kkrzysztofik/ASG_AirsoftCounter/docs/plans/2026-10-02-lipo-board-implementation.md

# LiPo Board (hardware) Implementation Plan

> **For Claude:** REQUIRED SUB-SKILL: Use superpowers:executing-plans to implement this plan task-by-task.

**Goal:** A JLCPCB-ready 2S/3S LiPo power board (`hardware/lipo.*`, `hardware/fab/lipo/`) generated by the
same flow as the carrier and the pack boards, as specified in `docs/plans/2026-10-02-lipo-board-design.md`.
LiPo firmware is out of scope (deferred with the pack firmware).

**Architecture:** A new board module `hardware/lipo.py`, selected by `BOARD=lipo` through `board.py`. It is
standalone (it shares almost nothing with the cell pack): it imports only footprint constants and `_tags`
from `pack.py`. Its own `check_power_path()` asserts the input -> fuse -> reverse FET -> TVS -> bucks order
and the EN wiring, next to the shared `board.check_structure`. Schematic, PCB, routing, ERC/DRC and the fab
package come from the existing generators unchanged.

**Tech stack:** Python 3 (`/usr/bin/python3`, needed for `pcbnew`), KiCad 9.0.8 (`kicad-cli`, pcbnew API),
Freerouting 2.4.1 (`hardware/tools/`), GNU make. JLCPCB parts API for stock checks.

**Conventions (read before starting):**
- Run everything from `hardware/`. Use `/usr/bin/python3` (`pcbnew` lives in the system Python).
- `rtk` rewrites some output; use plain `make`, `/usr/bin/grep -F`, `diff` when you need exact output.
- Every LCSC number is checked live before it goes into the module, and its comment records type
  (B = Basic, P = Preferred, E = Extended), maker part and date. Stock query:

  ```bash
  curl -sS -m 20 -X POST 'https://jlcpcb.com/api/overseas-pcb-order/v1/shoppingCart/smtGood/selectSmtComponentList' \
    -H 'Content-Type: application/json' -d '{"keyword":"TPS54302DDCR","currentPage":1,"pageSize":6}' \
    | /usr/bin/python3 -c 'import sys,json; [print(p["componentCode"],p["componentModelEn"],p["componentLibraryType"],p["stockCount"],p["componentSpecificationEn"]) for p in json.load(sys.stdin)["data"]["componentPageInfo"]["list"]]'
  ```
- Commit after every task. End commit messages with the attribution line in use for this repo.
- Pin numbers below come from the KiCad 9 symbols, checked 2026-10-02: TPS54302 1 GND, 2 SW, 3 VIN, 4 FB,
  5 EN, 6 BOOT; HT75xx-1-SOT89 1 GND, 2 VIN, 3 VOUT; AO3401A/BSS138 1 G, 2 S, 3 D; Device diodes 1 K, 2 A.
  STM32C071KBTx (LQFP32) pins reuse the roles variant A already checked: 4 VDD, 5 VSS, 6 NRST,
  7/8/9 PA0-PA2 (ADC), 13/14 I2C slave SDA/SCL, 15 PB0, 24 SWDIO, 25 SWCLK/BOOT0.

## Changes against the design doc (record them in it in L0.1)

- **Balance dividers always on**, no divider switch and no separate pack-total divider. With Basic
  megohm values they draw about 10 uA, next to the MCU's 85 uA Stop current; the top tap already is
  the pack total. Each ADC pin gets 100 nF so the STM32 ADC sees a low source impedance.
- **No reset/boot buttons and no status LED**: SWD pads only (a blank STM32C0 boots its ROM
  bootloader by itself). Saves the TACT and LED and their drain.
- **Bucks default ON when the key is on**: the kill FET's gate has a pull-down, so the bucks run with
  the MCU unflashed (bring-up) and the firmware latches them off.
- **Same inductor for both bucks if L0.1 confirms its saturation current** covers buck A's peaks
  (Heltec ~1 A at 27 dBm + amp 1.5 A, see `power_budget.py`); otherwise buck A gets its own part.

---

## Phase L0: part facts (gates the schematic)

### Task L0.1: Verify datasheet facts, record them in the design doc

No code. Output: a "Parts" section appended to `docs/plans/2026-10-02-lipo-board-design.md` (one row
per item: decision, source, date), the four changes above recorded, and its "Unverified" list trimmed.

Check and record (datasheet section or table for each):

1. **TPS54302** (C311983): VIN range and absolute max (expect 4.5-28 V, 30 V abs), VREF (expect 0.596 V),
   EN rising threshold, EN pull-up current and EN absolute max (the EN node sees up to
   13.05 V x 47k/147k = 4.2 V, more on a hot-plug spike), shutdown current, current limit, maximum duty
   cycle at 6 V in / 4.1 V out, recommended inductor and output capacitance for 4.1 V and 5.07 V.
2. **Feedback dividers:** buck A 30k/5k1 -> 0.596 x (1 + 30/5.1) = 4.10 V; buck B 75k/10k -> 5.07 V.
   Confirm both against VREF and the datasheet's allowed bottom-resistor range.
3. **Inductor:** `10uH 2A` (C2046332, Bourns SRN6045TA-100M) Isat and Irms against the TPS54302 current
   limit. If Isat is below about 3 A, pick a 10 uH part with Isat >= 3.5 A for buck A (`L_A`) and record it.
4. **HT7533-1** (C14289, Basic, SOT-89-3): VIN absolute max (must survive 3S full plus the hot-plug
   spike after the TVS), Iq, required input/output capacitors. If VIN max is below the TVS clamp,
   add a 1k series resistor before `C_LDO1` (the LDO draws microamps) and record why.
5. **AO3407A** (C15155): VDS -30 V, VGS +-20 V, RDS(on) at VGS -4.5 V (2S empty, about 6 V), pinout
   G-S-D the same as the AO3401A symbol used for it.
6. **SMBJ15A** (C113988): standoff 15 V (above 3S 12.6 V), clamp at the pack's hot-plug energy.
   Drawn with `Device:D_Zener` (unidirectional, K to the rail).
7. **BZT52C12** gate clamp (C43491, E): look for a Basic or Preferred 12 V SOD-123 zener first.
8. **Solder pads** `Connector_Wire:SolderWire-1sqmm_1x02_P5.4mm_D1.4mm_OD2.7mm`: 1 mm2 (17 AWG) is enough
   for the ~3 A worst case at 2S empty; a 14 AWG XT60 pigtail needs the 1.5 mm2 / 1.7 mm-drill
   variant. Pick one, record the lead gauge.
9. **B4B-XH-A** (balance): the carrier's C144395. Confirm a 3-pin XH plug seats in pins 1-3 of a
   4-pin header (keyed housing ramp on one side only); if not, fit B3B-XH-A + B4B-XH-A side by side.
10. **Divider values** (Basic 1M C17514, 470k C17709): tap1 470k/1M -> x0.680 (4.35 V -> 2.96 V),
   tap2 1M/470k -> x0.320 (8.70 V -> 2.78 V), tap3 2x1M/470k -> x0.190 (13.05 V -> 2.48 V). All below
   the 3.3 V ADC reference with HV-LiPo margin.

Commit: `docs: LiPo board part facts`.

---

## Phase L1: wire the board into the flow

### Task L1.1: `board.py` and the Makefile know `lipo`

**Files:** Modify `hardware/board.py:1-11`, `hardware/Makefile` (`boards` target).

**Step 1:** In `board.py` add `"lipo": "lipo"` to the module map and mention it in the docstring
(`BOARD=carrier (default), pack, pack_b or lipo`).

**Step 2:** In the Makefile `boards` target add `$(MAKE) BOARD=lipo all`, and `lipo` to the header comment.

**Step 3:** Verify it fails for the right reason:
Run: `BOARD=lipo /usr/bin/python3 -c "import board"`
Expected: `ModuleNotFoundError: No module named 'lipo'`.

No commit yet (the tree must stay buildable); commit with L2.1.

---

## Phase L2: board data (`hardware/lipo.py`)

### Task L2.1: The power-path check first

**Files:** Create `hardware/lipo.py`.

**Step 1:** Write the module skeleton with the check only and empty data:

```python
"""AirsoftCounter LiPo board: a 2S/3S airsoft LiPo instead of the 18650 pack. No charging.

Same role as pack.py: gen_sch.py / gen_pcb.py read it through board.py (BOARD=lipo), so run the
generators with `make BOARD=lipo ...`. Run this file to self-check (`/usr/bin/python3 lipo.py`).

check() runs board.check_structure plus check_power_path: pads -> fuse -> reverse P-FET -> TVS ->
both bucks and the LDO, both buck ENs on one node that the key pulls up and the MCU can pull down.
Source of truth: docs/plans/2026-10-02-lipo-board-design.md.
"""
import pack

NAME = "lipo"
TITLE = "AirsoftCounter v2 LiPo"

PARTS = {}
NETS = {}

def check_power_path():
    """Input order and the EN wiring the latched cutoff depends on."""
    net_of = {p: n for n, m in NETS.items() for p in m}
    assert net_of["J_IN1.1"] == net_of["F_IN1.1"], "input + not on the fuse"
    assert net_of["J_IN1.2"] == "GND", "input - not on GND"
    assert net_of["F_IN1.2"] == net_of["Q_REV1.3"], "fuse not on the reverse FET drain"
    assert net_of["Q_REV1.1"] == net_of["D_GZ1.2"] == net_of["R_REV1.1"], "FET gate clamp"
    vin = net_of["Q_REV1.2"]
    assert vin == "VIN", "reverse FET source is not VIN"
    for p in ("D_TVS1.1", "D_GZ1.1", "U_BA.3", "U_BB.3", "U_LDO.2", "R_EN1.1"):
        assert net_of[p] == vin, f"{p} not on VIN"
    assert net_of["U_BA.5"] == net_of["U_BB.5"] == net_of["R_EN2.1"] == net_of["Q_KILL.3"], \
        "buck ENs not on one node with the pull-down and the kill FET"
    assert net_of["R_EN1.2"] == net_of["J_KEY1.1"] and net_of["J_KEY1.2"] == net_of["U_BA.5"], \
        "key does not switch the EN pull-up"
    assert net_of["L_A.2"] == "VBAT_SW" and net_of["L_B.2"] == "+5V", "buck outputs swapped"
    assert net_of["R_GK.1"] == "GND", "kill gate pull-down missing (bucks must default on)"
    for i in (1, 2, 3):
        assert net_of[f"J_BAL1.{i + 1}"] == net_of[f"R_TT{i}.1"], f"tap {i} divider not on the plug"
        assert net_of[f"U_MCU.{6 + i}"] == f"TAP{i}_ADC", f"tap {i} not on its ADC pin"

def check():
    import sys

    import board  # pyright: ignore[reportMissingImports]  # local sibling module
    board.check_structure(sys.modules[__name__])
    check_power_path()
    print(f"lipo ok: {len(PARTS)} parts, {len(NETS)} nets")

if __name__ == "__main__":
    check_power_path()
```

**Step 2:** Run: `/usr/bin/python3 lipo.py`
Expected: `KeyError: 'J_IN1.1'` (no nets yet).

### Task L2.2: Parts, nets, LCSC

**Files:** Modify `hardware/lipo.py`.

**Step 1:** Replace `PARTS = {}` / `NETS = {}` with the data below. Values are from L0.1; if L0.1 changed
a part (inductor, zener, pads, LDO series resistor), use its result instead.

```python
R0805, C0805, SOT23, SOD123 = pack.R0805, pack.C0805, pack.SOT23, pack.SOD123
C1206, FUSE1206, LRN6045, LQFP32 = pack.C1206, pack.FUSE1206, pack.LRN6045, pack.LQFP32
XH2, XH6, MH, TP = pack.XH2, pack.XH6, pack.MH, pack.TP
XH4 = "Connector_JST:JST_XH_B4B-XH-A_1x04_P2.50mm_Vertical"
TSOT23_6 = "Package_TO_SOT_SMD:TSOT-23-6"
SOT89 = "Package_TO_SOT_SMD:SOT-89-3"
SMB = "Diode_SMD:D_SMB"
PADS = "Connector_Wire:SolderWire-1sqmm_1x02_P5.4mm_D1.4mm_OD2.7mm"

# ref: (value, symbol "lib:name", footprint "lib:name")
PARTS = {
    # --- input: XT60 pigtail on solder pads, fuse, reverse P-FET, TVS ---
    "J_IN1": ("LIPO", "Connector_Generic:Conn_01x02", PADS),     # hand-soldered pigtail
    "F_IN1": ("5A fuse", "Device:Fuse", FUSE1206),
    "Q_REV1": ("AO3407A", "Transistor_FET:AO3401A", SOT23),      # same G-S-D pinout (L0.1)
    "R_REV1": ("100k", *R0805),
    "D_GZ1": ("BZT52C12", "Device:D_Zener", SOD123),             # VGS clamp
    "D_TVS1": ("SMBJ15A", "Device:D_Zener", SMB),                # unidirectional TVS
    "C_VIN1": ("10uF", *C0805),
    "C_VIN2": ("10uF", *C0805),
    "C_VIN3": ("10uF", *C0805),
    "C_VIN4": ("10uF", *C0805),
    # --- buck A: VIN -> 4.10 V VBAT_SW (Heltec battery socket, amp) ---
    "U_BA": ("TPS54302DDCR", "Regulator_Switching:TPS54302", TSOT23_6),
    "C_BTA": ("100nF", *C0805),
    "L_A": ("10uH 2A", "Device:L", LRN6045),
    "R_FBA1": ("30k", *R0805),
    "R_FBA2": ("5k1", *R0805),
    "C_OA1": ("22uF 25V", "Device:C", C1206),
    "C_OA2": ("22uF 25V", "Device:C", C1206),
    # --- buck B: VIN -> 5.07 V +5V (LCD, LEDs, buzzer) ---
    "U_BB": ("TPS54302DDCR", "Regulator_Switching:TPS54302", TSOT23_6),
    "C_BTB": ("100nF", *C0805),
    "L_B": ("10uH 2A", "Device:L", LRN6045),
    "R_FBB1": ("75k", *R0805),
    "R_FBB2": ("10k", *R0805),
    "C_OB1": ("22uF 25V", "Device:C", C1206),
    "C_OB2": ("22uF 25V", "Device:C", C1206),
    # --- enable: key pulls EN up through R_EN1, R_EN2 pulls it down, the MCU's kill FET overrides ---
    "J_KEY1": ("KEY", "Connector_Generic:Conn_01x02", XH2),
    "R_EN1": ("100k", *R0805),
    "R_EN2": ("47k", *R0805),       # 6 V -> 1.92 V, 13.05 V -> 4.17 V on EN
    "Q_KILL": ("BSS138", "Transistor_FET:BSS138", SOT23),
    "R_GK": ("100k", *R0805),       # gate pull-down: bucks on until the MCU latches them off
    "R_KILL": ("1k", *R0805),
    # --- always-on 3.3 V and the MCU ---
    "U_LDO": ("HT7533-1", "Regulator_Linear:HT75xx-1-SOT89", SOT89),
    "C_LDO1": ("1uF", *C0805),
    "C_LDO2": ("1uF", *C0805),
    "U_MCU": ("STM32C071KBTx", "MCU_ST_STM32C0:STM32C071KBTx", LQFP32),
    "C_MCU1": ("100nF", *C0805),
    "C_MCU2": ("4u7", *C0805),
    "C_NRST": ("100nF", *C0805),
    "R_BOOT": ("10k", *R0805),
    "TP_SWDIO": ("SWDIO", "Connector:TestPoint", TP),
    "TP_SWCLK": ("SWCLK/BOOT0", "Connector:TestPoint", TP),
    "TP_NRST": ("NRST", "Connector:TestPoint", TP),
    "TP_3V3": ("3V3", "Connector:TestPoint", TP),
    "TP_GND": ("GND", "Connector:TestPoint", TP),
    # --- balance lead: one 4-pin XH takes a 2S (3-pin) plug in pins 1-3; tap 3 then reads 0 V ---
    "J_BAL1": ("BAL", "Connector_Generic:Conn_01x04", XH4),
    "R_TT1": ("470k", *R0805), "R_TB1": ("1M", *R0805),        # x0.680
    "R_TT2": ("1M", *R0805), "R_TB2": ("470k", *R0805),        # x0.320
    "R_TT3": ("1M", *R0805), "R_TT3B": ("1M", *R0805),         # 2M top in two parts
    "R_TB3": ("470k", *R0805),                                  # x0.190
    "C_TAP1": ("100nF", *C0805), "C_TAP2": ("100nF", *C0805), "C_TAP3": ("100nF", *C0805),
    # --- out to the carrier (same pinout as the pack boards) ---
    "J_PWR1": ("PWR", "Connector_Generic:Conn_01x06", XH6),
}
for i in range(1, 5):
    PARTS[f"H{i}"] = ("M3", "Mechanical:MountingHole", MH)

DNP = set()
NOT_ASSEMBLED = {"J_IN1", "TP_SWDIO", "TP_SWCLK", "TP_NRST", "TP_3V3", "TP_GND"}
# Unused MCU pins (all but supply, NRST, 3 ADC, I2C slave, kill, SWD).
NC_PINS = {f"U_MCU.{p}" for p in (1, 2, 3, 10, 11, 12, *range(16, 24), *range(26, 33))}
NC_PARTS = set()

LCSC = {
    ("100nF", C0805[1]): "C49678",      # B YAGEO CC0805KRX7R9BB104
    ("10uF", C0805[1]): "C15850",       # B Samsung CL21A106KAYNNNE 25V X5R
    ("4u7", C0805[1]): "C1779",         # B Samsung CL21A475KAQNNNE 25V X5R
    ("1uF", C0805[1]): "C28323",        # B Samsung CL21B105KBFNNNE 50V X7R
    ("22uF 25V", C1206): "C12891",      # B Samsung CL31A226KAHNNNE
    ("1M", R0805[1]): "C17514",         # B
    ("470k", R0805[1]): "C17709",       # B UNI-ROYAL 0805W8F4703T5E (2026-10-02)
    ("100k", R0805[1]): "C149504",      # B
    ("75k", R0805[1]): "C17819",        # P
    ("47k", R0805[1]): "C17713",        # B UNI-ROYAL 0805W8F4702T5E
    ("30k", R0805[1]): "C17621",        # B UNI-ROYAL 0805W8F3002T5E
    ("10k", R0805[1]): "C17414",        # B
    ("5k1", R0805[1]): "C27834",        # B
    ("1k", R0805[1]): "C17513",         # B
    ("5A fuse", FUSE1206): "C48332",    # E Bourns SF-1206F500-2
    ("AO3407A", SOT23): "C15155",       # E AOS AO3407A, 128k in stock (2026-10-02)
    ("BZT52C12", SOD123): "C43491",     # E BZT52C12 SOD-123 (2026-10-02; L0.1 looks for Basic)
    ("SMBJ15A", SMB): "C113988",        # E SMBJ15A DO-214AA, 135k in stock (2026-10-02)
    ("TPS54302DDCR", TSOT23_6): "C311983",  # E TI TPS54302DDCR, 65k in stock (2026-10-02)
    ("10uH 2A", LRN6045): "C2046332",   # E Bourns SRN6045TA-100M
    ("BSS138", SOT23): "C7420339",      # P
    ("HT7533-1", SOT89): "C14289",      # B Holtek HT7533-1 SOT-89-3, 109k in stock (2026-10-02)
    ("STM32C071KBTx", LQFP32): "C42116633",  # E
    ("KEY", XH2): "C158012",            # E JST B2B-XH-A(LF)(SN)
    ("BAL", XH4): "C144395",            # E JST B4B-XH-A(LF)(SN), carrier part
    ("PWR", XH6): "C144397",            # E JST B6B-XH-A(LF)(SN)
}

# net: [ "REF.pin", ... ]
NETS = {
    "LIPO_RAW": ["J_IN1.1", "F_IN1.1"],
    "LIPO_F": ["F_IN1.2", "Q_REV1.3"],
    "REV_G": ["Q_REV1.1", "D_GZ1.2", "R_REV1.1"],
    "VIN": ["Q_REV1.2", "D_GZ1.1", "D_TVS1.1", "C_VIN1.1", "C_VIN2.1", "C_VIN3.1", "C_VIN4.1",
            "U_BA.3", "U_BB.3", "U_LDO.2", "C_LDO1.1", "R_EN1.1"],
    "KEY_IN": ["R_EN1.2", "J_KEY1.1"],
    "BUCK_EN": ["J_KEY1.2", "U_BA.5", "U_BB.5", "R_EN2.1", "Q_KILL.3"],
    "KILL_G": ["Q_KILL.1", "R_GK.2", "R_KILL.2"],
    "KILL_DRV": ["R_KILL.1", "U_MCU.15"],
    # buck A
    "SW_A": ["U_BA.2", "L_A.1", "C_BTA.2"],
    "BOOT_A": ["U_BA.6", "C_BTA.1"],
    "FB_A": ["U_BA.4", "R_FBA1.2", "R_FBA2.1"],
    "VBAT_SW": ["L_A.2", "R_FBA1.1", "C_OA1.1", "C_OA2.1", "J_PWR1.3"],
    # buck B
    "SW_B": ["U_BB.2", "L_B.1", "C_BTB.2"],
    "BOOT_B": ["U_BB.6", "C_BTB.1"],
    "FB_B": ["U_BB.4", "R_FBB1.2", "R_FBB2.1"],
    "+5V": ["L_B.2", "R_FBB1.1", "C_OB1.1", "C_OB2.1", "J_PWR1.4"],
    # MCU
    "+3V3": ["U_LDO.3", "C_LDO2.1", "U_MCU.4", "C_MCU1.1", "C_MCU2.1", "TP_3V3.1"],
    "NRST": ["U_MCU.6", "C_NRST.1", "TP_NRST.1"],
    "BOOT0": ["U_MCU.25", "R_BOOT.1", "TP_SWCLK.1"],
    "SWDIO": ["U_MCU.24", "TP_SWDIO.1"],
    "SDA_EXT": ["U_MCU.13", "J_PWR1.5"],     # slave 0x30, pull-ups on the carrier
    "SCL_EXT": ["U_MCU.14", "J_PWR1.6"],
    "GND": ["J_IN1.2", "R_REV1.2", "D_TVS1.2", "C_VIN1.2", "C_VIN2.2", "C_VIN3.2", "C_VIN4.2",
            "U_BA.1", "U_BB.1", "R_FBA2.2", "R_FBB2.2", "C_OA1.2", "C_OA2.2", "C_OB1.2", "C_OB2.2",
            "R_EN2.2", "Q_KILL.2", "R_GK.1",
            "U_LDO.1", "C_LDO1.2", "C_LDO2.2",
            "U_MCU.5", "C_MCU1.2", "C_MCU2.2", "C_NRST.2", "R_BOOT.2", "TP_GND.1",
            "J_BAL1.1", "R_TB1.2", "R_TB2.2", "R_TB3.2", "C_TAP1.2", "C_TAP2.2", "C_TAP3.2",
            "J_PWR1.1", "J_PWR1.2"],
}
# Balance taps: plug pin i+1 -> top resistor -> ADC node (bottom resistor + 100 nF) -> PA0..PA2.
NETS["BAL1"] = ["J_BAL1.2", "R_TT1.1"]
NETS["BAL2"] = ["J_BAL1.3", "R_TT2.1"]
NETS["BAL3"] = ["J_BAL1.4", "R_TT3.1"]
NETS["TAP3_MID"] = ["R_TT3.2", "R_TT3B.1"]
for i in (1, 2, 3):
    top = "R_TT3B.2" if i == 3 else f"R_TT{i}.2"
    NETS[f"TAP{i}_ADC"] = [top, f"R_TB{i}.1", f"C_TAP{i}.1", f"U_MCU.{6 + i}"]
```

**Step 2:** Change the `__main__` guard to `check()`.

**Step 3:** Run: `/usr/bin/python3 lipo.py`
Expected: an `AttributeError` from `board.check_structure` for a layout name (`MODULES`) — the data
passes, the layout tables come in L3. Temporarily add `MODULES = {}`, `VARIANTS = {"standard": set()}`
and `assembled()` (copy `pack.assembled`) now; then expected: `lipo ok: 59 parts, 30 nets` (counts
may differ by the L0.1 changes).

**Step 4:** Break the check on purpose to prove it bites: swap `"U_BA.5"` out of `BUCK_EN`, run, see
`buck ENs not on one node`, put it back.

**Step 5:** Commit `board.py`, `Makefile`, `lipo.py`: `hardware: LiPo board parts and nets`.

---

## Phase L3: schematic

### Task L3.1: Schematic blocks and power flags

**Files:** Modify `hardware/lipo.py`.

Add the layout tables gen_sch.py reads, modelled on `pack.py:285-422`:

```python
NETCLASS_POWER = ("LIPO_*", "VIN", "VBAT_SW", "+5V", "SW_A", "SW_B")
RAILS = ("GND", "+3V3", "VIN", "VBAT_SW", "+5V")
PORT_LIB = {"GND": "power:GND", "+3V3": "power:+3V3", "VIN": "power:VDC",
            "VBAT_SW": "power:+BATT", "+5V": "power:+5V"}
_tags = pack._tags

BLOCKS = [
    {"title": "LiPo input: fuse, reverse FET, TVS", "at": (12.7, 12.7), "size": (127.0, 88.9),
     "parts": {"J_IN1": (12.7, 30.48, 0, None), "F_IN1": (35.56, 25.4, 0, None),
               "Q_REV1": (58.42, 30.48, 0, None), "R_REV1": (58.42, 55.88, 0, None),
               "D_GZ1": (76.2, 45.72, 0, None), "D_TVS1": (93.98, 45.72, 0, None),
               "C_VIN1": (106.68, 45.72, 0, None), "C_VIN2": (114.3, 45.72, 0, None),
               "C_VIN3": (106.68, 66.04, 0, None), "C_VIN4": (114.3, 66.04, 0, None)}},
    {"title": "Buck A 4.1 V (VBAT_SW), buck B 5.07 V (+5V)", "at": (152.4, 12.7),
     "size": (152.4, 139.7),
     "parts": {"U_BA": (30.48, 30.48, 0, None), "C_BTA": (55.88, 20.32, 0, None),
               "L_A": (76.2, 27.94, 0, None), "R_FBA1": (96.52, 38.1, 0, None),
               "R_FBA2": (96.52, 53.34, 0, None), "C_OA1": (114.3, 38.1, 0, None),
               "C_OA2": (127.0, 38.1, 0, None),
               "U_BB": (30.48, 91.44, 0, None), "C_BTB": (55.88, 81.28, 0, None),
               "L_B": (76.2, 88.9, 0, None), "R_FBB1": (96.52, 99.06, 0, None),
               "R_FBB2": (96.52, 114.3, 0, None), "C_OB1": (114.3, 99.06, 0, None),
               "C_OB2": (127.0, 99.06, 0, None)},
     "tags": _tags(["BUCK_EN"], 12.7, 127.0)},
    {"title": "Key enable, MCU kill, J_PWR1", "at": (12.7, 114.3), "size": (127.0, 88.9),
     "parts": {"J_KEY1": (12.7, 20.32, 0, None), "R_EN1": (35.56, 20.32, 0, None),
               "R_EN2": (55.88, 35.56, 0, None), "Q_KILL": (76.2, 40.64, 0, None),
               "R_GK": (66.04, 60.96, 0, None), "R_KILL": (50.8, 50.8, 0, None),
               "J_PWR1": (106.68, 35.56, 0, None)},
     "tags": _tags(["BUCK_EN", "KILL_DRV", "SDA_EXT", "SCL_EXT"], 12.7, 76.2)},
    {"title": "Always-on 3V3, STM32C071, SWD pads", "at": (317.5, 12.7), "size": (139.7, 152.4),
     "parts": {"U_LDO": (30.48, 20.32, 0, None), "C_LDO1": (12.7, 30.48, 0, None),
               "C_LDO2": (50.8, 30.48, 0, None),
               "U_MCU": (60.96, 88.9, 0, None),
               "C_MCU1": (17.78, 58.42, 0, None), "C_MCU2": (17.78, 76.2, 0, None),
               "C_NRST": (17.78, 93.98, 0, None), "R_BOOT": (17.78, 111.76, 0, None),
               "TP_NRST": (106.68, 50.8, 0, None), "TP_SWCLK": (106.68, 60.96, 0, None),
               "TP_SWDIO": (106.68, 71.12, 0, None), "TP_3V3": (106.68, 81.28, 0, None),
               "TP_GND": (106.68, 91.44, 0, None)},
     "fields": {r: {"Reference": (5.08, -2.54, "left"), "Value": (5.08, 2.54, "left")}
                for r in ("TP_NRST", "TP_SWCLK", "TP_SWDIO", "TP_3V3", "TP_GND")},
     "tags": _tags(["TAP1_ADC", "TAP2_ADC", "TAP3_ADC", "KILL_DRV", "SDA_EXT", "SCL_EXT",
                    "NRST", "BOOT0", "SWDIO"], 12.7, 127.0, per_row=5)},
    {"title": "Balance lead dividers", "at": (152.4, 165.1), "size": (152.4, 76.2),
     "parts": {"J_BAL1": (12.7, 30.48, 0, None),
               "R_TT1": (40.64, 20.32, 0, None), "R_TB1": (40.64, 40.64, 0, None),
               "C_TAP1": (55.88, 40.64, 0, None),
               "R_TT2": (76.2, 20.32, 0, None), "R_TB2": (76.2, 40.64, 0, None),
               "C_TAP2": (91.44, 40.64, 0, None),
               "R_TT3": (111.76, 12.7, 0, None), "R_TT3B": (111.76, 27.94, 0, None),
               "R_TB3": (111.76, 45.72, 0, None), "C_TAP3": (127.0, 45.72, 0, None)},
     "tags": _tags(["TAP1_ADC", "TAP2_ADC", "TAP3_ADC"], 12.7, 63.5)},
    {"title": "Mounting holes and power flags", "at": (317.5, 177.8), "size": (139.7, 50.8),
     "parts": {"H1": (7.62, 16.51, 0, None), "H2": (22.86, 16.51, 0, None),
               "H3": (38.1, 16.51, 0, None), "H4": (53.34, 16.51, 0, None)},
     "flags": [("GND", 10.16, 36.83), ("VIN", 33.02, 36.83), ("VBAT_SW", 55.88, 36.83),
               ("+5V", 78.74, 36.83)]},
]
```

The coordinates are a starting point: `gen_sch.py` reports clashes with their location.

**Step:** `make BOARD=lipo sch`. Move parts until `gen_sch.py` and `check_netlist.py` pass. Commit
`hardware: LiPo board schematic`.

### Task L3.2: ERC clean

**Step:** `kicad-cli sch erc --severity-all --exit-code-violations -o build/lipo_erc.rpt lipo.kicad_sch`.
Expected: 0 violations. Typical fixes, as on the pack: a PWR_FLAG for a rail driven only by passive
pins (`flags`), an `NC_PINS` entry, a symbol whose pin type needs a driver. Do not silence ERC by
changing pin types. Commit.

---

## Phase L4: PCB

### Task L4.1: Outline and placement

**Files:** Modify `hardware/lipo.py`.

Add the PCB tables, modelled on `pack.py:428-553`. Start at 50 x 40 mm, single-side SMD on top:

```python
W, H, CORNER = 50.0, 40.0, 2.0
NETCLASS_EXPECT = (("VIN", [0.8, 0.2]), ("VBAT_SW", [0.8, 0.2]), ("+5V", [0.8, 0.2]),
                   ("SW_A", [0.8, 0.2]), ("GND", [0.25, 0.2]), ("SDA_EXT", [0.25, 0.2]))
DRC_RULES = {}
BOTTOM = set()
# Left edge: LiPo pads. Right edge: J_PWR1 and J_KEY1. Top edge: J_BAL1. Bucks in the middle with
# their input caps between them; MCU and dividers in the lower-left, away from the switch nodes.
PLACE = {
    "J_IN1": (4.5, 20, 90),
    "F_IN1": (10, 12, 0), "Q_REV1": (10, 17, 0), "R_REV1": (10, 21, 0), "D_GZ1": (10, 25, 0),
    "D_TVS1": (16, 12, 90),
    "C_VIN1": (21, 8, 0), "C_VIN2": (21, 11, 0), "C_VIN3": (21, 23, 0), "C_VIN4": (21, 26, 0),
    "U_BA": (26, 9.5, 0), "C_BTA": (26, 5, 0), "L_A": (33, 9, 0),
    "R_FBA1": (26, 14, 0), "R_FBA2": (29.5, 14, 0), "C_OA1": (39, 6, 90), "C_OA2": (39, 12, 90),
    "U_BB": (26, 24.5, 0), "C_BTB": (26, 20, 0), "L_B": (33, 25, 0),
    "R_FBB1": (26, 29, 0), "R_FBB2": (29.5, 29, 0), "C_OB1": (39, 22, 90), "C_OB2": (39, 28, 90),
    "J_PWR1": (46, 20, 90), "J_KEY1": (46, 33, 90),
    "R_EN1": (41, 33, 0), "R_EN2": (41, 36, 0), "Q_KILL": (36, 34, 0),
    "R_GK": (32, 36, 0), "R_KILL": (32, 33, 0),
    "U_LDO": (15, 31, 0), "C_LDO1": (10, 30, 0), "C_LDO2": (10, 33, 0),
    "U_MCU": (21, 33.5, 0), "C_MCU1": (16, 36, 0), "C_MCU2": (26, 36, 0),
    "C_NRST": (26, 31.5, 0), "R_BOOT": (16, 38, 0),
    "TP_SWDIO": (4, 31, 0), "TP_SWCLK": (4, 34, 0), "TP_NRST": (4, 37, 0),
    "TP_3V3": (7, 37, 0), "TP_GND": (7, 34, 0),
    "J_BAL1": (12, 3, 0),
    "R_TT1": (5, 8, 0), "R_TB1": (5, 11, 0), "C_TAP1": (5, 14, 0),
    "R_TT2": (14, 6, 0), "R_TB2": (14, 9, 0), "C_TAP2": (14, 12, 0),
    "R_TT3": (17, 6, 0), "R_TT3B": (17, 9, 0), "R_TB3": (17, 12, 0), "C_TAP3": (17, 15, 0),
    "H1": (3.5, 3.5, 0), "H2": (46.5, 3.5, 0), "H3": (3.5, 36.5, 0), "H4": (46.5, 36.5, 0),
}
REF_AT = {}
HIDE_REF = ("TP_SWDIO", "TP_SWCLK", "TP_NRST", "TP_3V3", "TP_GND")
LABELS = {}
TEXTS = [("AirsoftCounter v2 LiPo", 25, 1.8, 0, 1.0, True), ("2026-10", 25, 38.5, 0, 1.0, True),
         ("LIPO 2S/3S", 2.5, 20, 90, 0.8, False), ("PWR", 43.5, 20, 90, 0.8, False),
         ("KEY", 43.5, 33, 90, 0.8, False), ("BAL", 12, 6.5, 0, 0.8, False)]
GND_VIAS = []
HELTEC_PADS = {}
SIZE_MM = (W, H)
NPTH_XY = sorted((PLACE[r][0], PLACE[r][1]) for r in ("H1", "H2", "H3", "H4"))
```

These positions are first guesses; expect to move many parts.

**Step 1:** `make BOARD=lipo pcb`. Expect `wrote lipo.kicad_pcb`. Open it in pcbnew, fix overlaps in
`PLACE` (and grow `W`/`H` if it cannot fit; 60 x 45 mm is fine), regenerate. Rules: each buck's input
caps within 3 mm of its VIN/GND pins, SW node short, the feedback divider on the quiet side away from
`L_A`/`L_B`, the ADC dividers and MCU away from the switch nodes.

**Step 2:** Commit `hardware: LiPo board placement`.

### Task L4.2: Route, DRC, fab

**Step 1:** `make BOARD=lipo check` (Freerouting, then ERC + DRC with schematic parity). Fix placement
until DRC is clean; do not relax rules except where a stock footprint forces it (record why in a
comment, like `pack.DRC_RULES`).

**Step 2:** `make BOARD=lipo fab`. `check_gerbers.py` must pass (size, 4 mounting holes; the solder pad
drill must be >= the 0.8 mm `PTH_COMPONENT_MIN` default). `jlc.py` writes `fab/lipo/jlc_bom.csv` and
`jlc_cpl.csv`; confirm `J_IN1` and the test pads are not in the BOM.

**Step 3:** Look at `fab/lipo/top.png` and print `fab/lipo/print_1to1.pdf` at 100 %: check the XT60
lead fits the pads and a real balance plug fits `J_BAL1`, as was done for the pack holders.

**Step 4:** `make boards` to confirm the carrier and both pack boards still build. Commit
`hardware: LiPo board routed, fab package`.

---

## Phase L5: docs

### Task L5.1: Design doc, ordering notes

**Files:** Modify `docs/plans/2026-10-02-lipo-board-design.md`, `hardware/fab/ORDERING.md`.

- Design doc: status line -> "hardware generated (`make BOARD=lipo all` into `fab/lipo/`)"; Extended
  part types per order (count them from `jlc_bom.csv`); key-off drain with the always-on dividers.
- `ORDERING.md`: a LiPo board section (upload `fab/lipo/lipo_gerbers_jlcpcb.zip` + the two CSVs; the
  pigtail and test pads are hand-soldered; order an XT60 female pigtail, 1 mm2 or as L0.1 decided).
- Bring-up order for the doc: bench supply at 7.4 V with a 100 mA limit on the pads, key open -> only
  the LDO runs (3.3 V on `TP_3V3`, input current a few hundred uA with a blank MCU); key closed ->
  4.10 V and 5.07 V; reversed supply -> no current; then a real 2S and a real 3S pack.

Commit `docs: LiPo board generated`.

---

## Done when

- `make BOARD=lipo all` is green (check, ERC, DRC with parity, gerber check, JLC CSVs).
- `make boards` is green for all four boards.
- `/usr/bin/python3 lipo.py` prints `lipo ok`.
- The design doc records the part facts, the four plan-time changes and what is still unverified.
