kkrzysztofik/ASG_AirsoftCounter/docs/plans/2026-10-01-pack-board-implementation.md

# Pack Board (hardware) Implementation Plan

> **For Claude:** REQUIRED SUB-SKILL: Use superpowers:executing-plans to implement this plan task-by-task.

**Goal:** A JLCPCB-ready 4x18650 pack board (`hardware/pack.*`, `hardware/fab/pack/`) generated by the same
flow as the carrier, plus the carrier with its power section moved off (6-pin `J_PWR1`), as specified in
`docs/plans/2026-10-01-pack-board-design.md`. Pack firmware is out of scope (deferred by the user).

**Architecture:** The generators (`gen_sch.py`, `gen_pcb.py`, `route.py`, `jlc.py`, `check_*.py`) become
board-agnostic: a `BOARD` environment variable picks the board module (`design.py` = carrier, `pack.py` = pack),
and every board-specific table (schematic blocks, placements, labels, outline, Gerber expectations) moves into
that module. The refactor is proven by a byte-identical regenerate of the unrouted carrier. The pack board is then
a new data module plus layout, and the carrier change is a data edit plus re-layout.

**Tech stack:** Python 3 (`/usr/bin/python3`, needed for `pcbnew`), KiCad 9.0.8 (`kicad-cli`, pcbnew API),
Freerouting 2.4.1 (`hardware/tools/`), GNU make. JLCPCB parts API for stock checks.

**Conventions (read before starting):**
- Run everything from `hardware/`. Use `/usr/bin/python3` (not a venv python: `pcbnew` lives in the system one).
- `rtk` wraps shell commands but rewrites some output; use plain `make`, `/usr/bin/grep -F`, `diff`, `cmp`
  when you need exact output.
- Every LCSC number is checked live against the JLCPCB API before it goes into a module, and its comment
  records type (B/P/E), maker part and date, like `design.py`'s `LCSC` table. Stock query:

  ```bash
  curl -sS -m 20 -X POST 'https://jlcpcb.com/api/overseas-pcb-order/v1/shoppingCart/smtGood/selectSmtComponentList' \
    -H 'Content-Type: application/json' -d '{"keyword":"XC6206P332MR","currentPage":1,"pageSize":6}' \
    | /usr/bin/python3 -c 'import sys,json; [print(p["componentCode"],p["componentModelEn"],p["componentLibraryType"],p["stockCount"],p["componentSpecificationEn"]) for p in json.load(sys.stdin)["data"]["componentPageInfo"]["list"]]'
  ```
- Commit after every task. End commit messages with the attribution line in use for this repo.

---

## Phase P0: part facts (gates the schematic)

### Task P0.1: Verify datasheet facts and pick the remaining parts

No code. Output: a "Parts" section appended to `docs/plans/2026-10-01-pack-board-design.md` (one row per
item: decision, source, date) and the "Unverified" list there trimmed to what is still open.

Settle each item from its datasheet (record the URL/document and section):

1. **STM32C071KBT6** (LCSC C42116633, the LQFP32_GP pinout, KiCad symbol `MCU_ST_STM32C0:STM32C071KBTx`):
   - ROM DFU over USB on PA11/PA12 (AN2606, STM32C071 section) and whether the factory `nBOOT_SEL` setting
     samples the PA14-BOOT0 pin. If the pin is ignored by default, the board still works (blank chip boots
     DFU by the empty-flash check) but write that down; the BOOT0 button then only matters after an option-byte
     change.
   - Crystal-less USB needs HSI48 + CRS (no crystal parts).
   - Internal DP pull-up exists (no external 1.5k).
   - Stop-mode current with RTC/LSI wake-up.
2. **BQ25601** (C468236): application-circuit values (inductor, PMID/SYS/BAT/REGN/BTST caps), default ICHG
   and VREG, PSEL meaning, TS divider for a 10k B3435 NTC (RT1/RT2 from REGN), /QON handling, behaviour of
   STAT. Pick the inductor (current rating >= 3 A, LCSC stocked).
3. **INA3221** (C181255): A0 address straps (GND = 0x40, VS = 0x41), handling of unused channels (cell 4
   uses INA_B ch1; ch2/ch3 spare), VPU connection, input common-mode and the negative input limit (relevant to
   the crowbar event: -0.3 V abs min), recommended input filter resistor (<= 10 Ohm).
4. **XB8089D** (C79928): overcurrent trip current, release behaviour. Pick the per-cell **fuse** above that
   trip (about 5 A fast-blow, 1206 or 2410, LCSC stocked) and confirm SS34 (C8678) surge current covers the
   crowbar until the fuse clears (compare fuse I2t at about 20-30 A with the SS34 8.3 ms surge rating).
5. **LDO:** XC6206P332MR (expected C5446, Basic): Iq about 1 uA, Vin max 6 V, 200 mA. Confirm.
6. **AO3401A** (C15127, Basic): RDS(on) at VGS = -2.5 V / -3.0 V. **BSS138** (C7420339, already used).
   **BAT54C** (expect C47546 or similar, Basic). **Shunt 20 mOhm** 0805/1206 1% (pick LCSC).
   **NTC 10k B3435 0805** (pick LCSC). **Tact switch** SMD for BOOT0 and NRST (pick a Basic one).
   **LEDs** 0805 (Basic) for STAT and the MCU status LED.
7. **USB-C receptacle**: the KiCad footprint `Connector_USB:USB_C_Receptacle_HCTL_HC-TYPE-C-16P-01A` with
   symbol `Connector:USB_C_Receptacle_USB2.0_14P`; find its LCSC number and stock.
8. **6-pin XH**: JST B6B-XH-A (LCSC number, stock), footprint
   `Connector_JST:JST_XH_B6B-XH-A_1x06_P2.50mm_Vertical`.
9. **18650 holder**: Keystone 1042 (footprint `Battery:BatteryHolder_Keystone_1042_1x18650`) or MPD
   BH-18650-PC; holder is hand-soldered, not in the JLC BOM (add it to `fab/OFFBOARD_PARTS.md`). Note the
   courtyard size: it fixes the board outline in P3.
10. **Gate resistor:** the design says 100k gate-to-source; at -4.2 V that is 42 uA per closed switch,
    170 uA for four, which breaks the "tens of uA" quiescent target. Use **1 MOhm** (4 uA each). Update the
    design doc's per-cell diagram.

Commit: `docs: pack board part facts (P0)`.

---

## Phase P1: board-agnostic generators (carrier output must not change)

### Task P1.1: Baseline snapshot of the unrouted carrier

**Step 1:** From a clean tree:

```bash
cd hardware && make pcb && mkdir -p /tmp/carrier_base \
  && cp carrier.kicad_sch carrier.kicad_pro carrier.kicad_pcb /tmp/carrier_base/
```

**Step 2:** Restore the committed (routed) files: `git checkout -- carrier.kicad_pcb carrier.kicad_sch carrier.kicad_pro`.

This snapshot is the regression oracle for every P1 task: after each one, `make pcb` must reproduce these
three files exactly.

**Step 3:** Write the check script `hardware/tools/same_as_base.sh`:

```bash
#!/bin/sh
# Regenerate the unrouted carrier and compare with the P1 baseline, then restore the routed files.
set -e
cd "$(dirname "$0")/.."
make pcb >/dev/null
for f in carrier.kicad_sch carrier.kicad_pro carrier.kicad_pcb; do cmp "$f" "/tmp/carrier_base/$f"; done
git checkout -- carrier.kicad_pcb carrier.kicad_sch carrier.kicad_pro
echo "carrier unchanged"
```

Run it once on the untouched tree: expect `carrier unchanged`. (If `cmp` differs here the generators are not
deterministic; stop and find out why before going on.)

This is a temporary tool; delete it in P1.5.

### Task P1.2: `board.py` selects the board module

**Files:** create `hardware/board.py`; modify the `import design` line in `gen_sch.py`, `gen_pcb.py`,
`check_netlist.py`, `jlc.py`.

```python
"""Pick the board module the generators work on: BOARD=carrier (default, design.py) or BOARD=pack (pack.py)."""
import importlib
import os

NAME = os.environ.get("BOARD", "carrier")
design = importlib.import_module({"carrier": "design", "pack": "pack"}[NAME])
```

In each generator replace `import design` with `from board import design`. Run `tools/same_as_base.sh`;
expect `carrier unchanged`. Commit.

### Task P1.3: Move board tables into the board module

Move, verbatim, into `design.py` (bottom of the file, under a `# --- layout (read by gen_sch.py / gen_pcb.py)`
header), and reference them as `design.X` from the generators:

| From | Names |
|---|---|
| `gen_sch.py` | `_driver`, `BLOCKS`, `RAILS`, `PORT_LIB`, `NC_PARTS`, `NC_PINS`, the `netclass_patterns` list in `project()` (as `NETCLASS_POWER = ("VBAT*", "BAT_N", "+5V", "SW")`) |
| `gen_pcb.py` | `W`, `H`, `CORNER`, `PLACE`, `REF_AT`, `LABELS`, `TEXTS`, `GND_VIAS`, `HELTEC_PADS`, the net/width list in `verify()` (as `NETCLASS_EXPECT`) |
| `check_gerbers.py` | `SIZE_MM` (derive from `W`, `H`), `NPTH_XY` (derive from the `H1..H4` entries of `PLACE`) |

Add `NAME = "carrier"` and `TITLE = "AirsoftCounter v2 carrier"` to `design.py`.

Heltec-only PCB steps in `gen_pcb.build()` (the `HELTEC_PADS` assertion and the `HELTEC_UNDER` / `ANT`
rule areas) run only `if design.HELTEC_PADS:`.

Replace every literal `carrier` file stem in `gen_sch.py` (output names, `instances()` project name, `.kicad_pro`
meta filename, `carrier_bad.kicad_sch`), `gen_pcb.py` (`PCB`, `SetSheetfile`), `route.py` (temp names may
stay), `check_netlist.py` (`XML`), `check_gerbers.py` (`EXPECTED`, default zip path) and `jlc.py` (`PCB`, `ZIP`)
with `design.NAME`.

Run `tools/same_as_base.sh` after each file; expect `carrier unchanged`. Commit.

### Task P1.4: Split `design.check()` into a shared part and a carrier part

**Files:** `board.py`, `design.py`.

Move the board-independent checks from `design.check()` into `board.check_structure(m)` (unique pins, known
parts, no single-pin nets, DNP known, no unconnected non-mechanical part, LCSC complete and not stale for
`m.assembled()`, MODULES/VARIANTS refer to known names). `design.check()` calls it and keeps the Heltec header
checks and the "variant needs an input" rule.

`jlc.py`: the default variant is the first key of `design.VARIANTS` (carrier: `deluxe`, unchanged file names).

**Test first:** add to `board.py`

```python
if __name__ == "__main__":
    import types
    bad = types.SimpleNamespace(PARTS={"R1": ("1k", "Device:R", "fp")}, NETS={"A": ["R1.1"]}, DNP=set(),
                                LCSC={}, MODULES={}, VARIANTS={"x": set()}, assembled=lambda v="x": ["R1"])
    try:
        check_structure(bad)
    except AssertionError as e:
        assert "single pin" in str(e), e
    else:
        raise SystemExit("check_structure accepted a single-pin net")
    print("board.py self-check ok")
```

Run `/usr/bin/python3 board.py` before writing `check_structure` (expect `AttributeError`/`NameError`), then
after (expect `board.py self-check ok`). Then `tools/same_as_base.sh`. Commit.

### Task P1.5: Makefile takes `BOARD`

**Files:** `hardware/Makefile`.

- `BOARD ?= carrier`, `export BOARD`; every `carrier.*` becomes `$(BOARD).*`; `ZIP = fab/$(BOARD)/...` only for
  the pack. Keep the carrier's existing paths: use `FAB = fab` for carrier and `FAB = fab/pack` for pack
  (`ifeq ($(BOARD),carrier)`), so no carrier output moves.
- `build/` intermediates get the board name (`build/$(BOARD).xml`, `build/$(BOARD)_erc.rpt`, ...).
- New target `boards`: `$(MAKE) BOARD=carrier all && $(MAKE) BOARD=pack all`.

Run `tools/same_as_base.sh` (expect `carrier unchanged`), then a full `make all` and check that
`git status --short` shows only the files you edited (routed board, Gerbers, CSVs may differ by routing; if they
do, restore them with `git checkout` and note it in the commit message). Delete `tools/same_as_base.sh`.
Commit: `hardware: board-agnostic generators (BOARD=carrier|pack)`.

---

## Phase P2: pack board data (`hardware/pack.py`)

### Task P2.1: Branch-order check first

**Files:** create `hardware/pack.py` with `NAME = "pack"`, empty `PARTS`/`NETS`, and a `check()` that calls
`board.check_structure` and then `check_branches()`:

```python
def check_branches():
    """Every cell: holder+ -> fuse -> shunt -> back-to-back P-FET -> pack rail, in that order (design doc)."""
    net_of = {p: n for n, m in NETS.items() for p in m}
    for i in range(1, 5):
        assert net_of[f"BT{i}.1"] == net_of[f"F{i}.1"], f"cell {i}: holder+ not on fuse"
        assert net_of[f"F{i}.2"] == net_of[f"R_SH{i}.1"] == net_of[f"U_INA{(i - 1) // 3 + 1}.{INA_IN[i][0]}"], f"cell {i}: fuse -> shunt / IN+"
        assert net_of[f"R_SH{i}.2"] == net_of[f"Q_A{i}.3"] == net_of[f"U_INA{(i - 1) // 3 + 1}.{INA_IN[i][1]}"], f"cell {i}: shunt -> FET / IN-"
        assert net_of[f"Q_A{i}.2"] == net_of[f"Q_B{i}.2"], f"cell {i}: FET sources not common"
        assert net_of[f"Q_B{i}.3"] == "VPACK", f"cell {i}: FET not on the pack rail"
        assert net_of[f"BT{i}.2"] == net_of[f"U_P{i}.5"], f"cell {i}: holder- not on XB8089D BAT-"
```

(`INA_IN` maps cell -> INA3221 (IN+, IN-) pin numbers: cell 1 -> ("12", "11"), 2 -> ("15", "14"),
3 -> ("2", "1"), 4 -> ("12", "11") on `U_INA2`.) Pin numbers for the XB8089D come from `local:XB8089D` (carrier:
pins 5/7/8/9 = BAT-, 1-4 = VM/GND, 6 = VDD).

Run `/usr/bin/python3 pack.py`: expect a `KeyError` (no parts yet). Don't commit; P2.2 makes it pass.

### Task P2.2: Parts and nets

Write `PARTS`, `NETS`, `LCSC`, `DNP`, `MODULES = {}`, `VARIANTS = {"standard": set()}`, `assembled()` in
`pack.py`, following `design.py`'s style (generate per-cell parts in a loop, like `DRIVERS`). Values come
from P0. The netlist:

**Per cell i = 1..4** (refs suffixed with i):

| Part | Value | Pins |
|---|---|---|
| `BTi` | 18650 holder (DNP-in-BOM: hand-soldered, `LCSC` has no entry, add to `NOT_ASSEMBLED`) | 1 = +, 2 = - |
| `Fi` | ~5 A fast fuse | 1 `CELLi_RAW`, 2 `CELLi_F` |
| `D_CBi` | SS34 crowbar | K `CELLi_F`, A `CELLi_N` |
| `R_SHi` | 20 mOhm | 1 `CELLi_F`, 2 `CELLi_S` |
| `Q_Ai`, `Q_Bi` | AO3401A | Q_A: D `CELLi_S`, S `CELLi_SRC`, G `CELLi_G`; Q_B: D `VPACK`, S `CELLi_SRC`, G `CELLi_G` |
| `R_GSi` | 1M | `CELLi_G` - `CELLi_SRC` |
| `Q_Ni` | BSS138 | D `CELLi_G`, S `GND`, G `SWi_G` |
| `R_PDi` | 100k | `SWi_G` - `GND` (switch off while the MCU is unpowered or in reset) |
| `R_SWi` | 1k | MCU pin - `SWi_G` |
| `R_BYPi` | 0R **DNP** | `CELLi_S` - `VPACK` (bring-up bypass) |
| `U_Pi` | XB8089D | BAT- (5,7,8,9) `CELLi_N`, VM (1-4) `GND`, VDD (6) `PROTi_VDD` |
| `R_PROTi`, `C_PROTi` | 1k, 100nF | `CELLi_F` - `PROTi_VDD` - `CELLi_N` (as on the carrier) |
| `TH_i` | NTC 10k | `NTC_PWR` - `NTCi`; with `R_NTCi` 10k `NTCi` - `GND` |

Holder pins: `BTi.1` on `CELLi_RAW`, `BTi.2` on `CELLi_N`.

**Shared:**
- Diode-OR to the LDO: `D_OR1` (BAT54C) anodes `CELL1_F`, `CELL2_F`; `D_OR2` anodes `CELL3_F`, `CELL4_F`;
  `D_OR3` both anodes `SYS` (so the MCU runs from USB with no cells, for DFU). All cathodes: `VMCU_IN`.
- `U_LDO` XC6206P332MR: VI `VMCU_IN`, VO `+3V3`, GND; `C_LDO1`/`C_LDO2` 1 uF in/out.
- `U_INA1` (A0 = GND, 0x40): cells 1-3. `U_INA2` (A0 = VS, 0x41): cell 4 on ch1; ch2/ch3 handled as P0 says.
  VS and VPU on `+3V3`, 100 nF each. SCL/SDA on `SCL_INT`/`SDA_INT`. CRITICAL of both on `INA_CRIT`, WARNING
  of both on `INA_WARN` (open drain, 10k pull-ups to `+3V3`). If P0 recommends input filter resistors, add
  them (and move the IN+/IN- pins in `check_branches` to the resistor's far side).
- `U_CHG` BQ25601: VBUS/VAC `VBUS`, PMID, SW, BTST, REGN, SYS `SYS`, BAT `VPACK`, TS from the REGN divider
  with `TH_CHG` (5th NTC), PSEL per P0, /CE `CHG_CE` (10k pull-down: charging enabled with the MCU off), /INT
  `CHG_INT` (10k pull-up), STAT via `R_STAT` + `LED_STAT` to `+3V3` (P0: confirm STAT sink rating), /PG unused
  (no-connect), /QON no-connect if P0 allows, SCL/SDA on the internal bus. Caps and inductor from P0.
- `J_USB1` USB-C: VBUS pins `VBUS`, GND, CC1/CC2 each 5.1k to GND (`R_CC1`, `R_CC2`), D+ (A6, B6) `USB_DP`,
  D- (A7, B7) `USB_DM`, shield to GND.
- `U_MCU` STM32C071KBTx: VDD (4) `+3V3` with 100 nF + 4.7 uF; VSS (5) GND; PF2-NRST (6) `NRST` with 100 nF
  to GND and `SW_RST` to GND; PA14-BOOT0 (25) `BOOT0` with `SW_BOOT` to `+3V3` and 10k pull-down; PA13 (24)
  `SWDIO`; test pads `TP_SWDIO`, `TP_SWCLK` (=`BOOT0`), `TP_NRST`, `TP_GND`. Pin map:

  | Signal | Pin |
  |---|---|
  | USB_DM / USB_DP | PA11 (22) / PA12 (23) |
  | I2C1 internal SCL / SDA | PB6 (30) / PB7 (31), 4.7k pull-ups to `+3V3` |
  | I2C2 external SCL / SDA | PA7 (14) / PA6 (13), **no pull-ups** |
  | NTC1..4 (ADC) | PA0..PA3 (7-10) |
  | NTC_PWR | PA4 (11) |
  | SW1..SW4 gate drive | PB0 (15), PB1 (16), PB2 (17), PA8 (18) |
  | CHG_CE / CHG_INT | PA5 (12) / PB3 (27) |
  | INA_CRIT / INA_WARN | PB4 (28) / PB5 (29) |
  | Status LED (via 1k) | PA15 (26) |

  Unused pins (PB8, PB9, PC14, PC15, PA9, PA10, PC6) get no-connect flags (`NC_PINS`).
- Power out: `J_KEY1` (4-pin XH, pins 1-2) `SYS` -> `KEY_OUT`; `F_SYS1` (the carrier's 2A PTC, C22374899)
  `KEY_OUT` -> `VBAT_SW`; boost `U1`, `L1`, `D1`, `R_FB1/2`, `C_IN1`, `C_OUT1/2` copied from `design.py`
  with the same values and LCSC numbers.
- `J_PWR1` B6B-XH-A: 1-2 `GND`, 3 `VBAT_SW`, 4 `+5V`, 5 `SDA_EXT`, 6 `SCL_EXT`.
- `H1..H4` M3 holes.

**Step:** run `/usr/bin/python3 pack.py`. Expect `design ok`-style output from `check()` with
`check_branches()` passing. Break one link on purpose (swap `R_SH1.1`/`R_SH1.2`), confirm the assertion names
cell 1, undo. Commit: `hardware: pack board netlist (pack.py)`.

---

## Phase P3: pack schematic

### Task P3.1: Schematic blocks

**Files:** `pack.py` (layout section): `BLOCKS`, `RAILS = ("GND", "+3V3", "+5V", "VBAT_SW", "VPACK")`,
`PORT_LIB` (reuse `power:+BATT`-style stock symbols, e.g. `power:VDC` for `VPACK`; check it exists in
`/usr/share/kicad/symbols/power.kicad_sym`), `NC_PARTS`, `NC_PINS`, `NETCLASS_POWER =
("VBAT*", "VPACK", "SYS", "VBUS", "CELL*_RAW", "CELL*_F", "CELL*_S", "CELL*_SRC", "CELL*_N", "+5V", "SW*")`.

Blocks (one per sheet area, sized like the carrier's): USB-C + charger; cells 1-2; cells 3-4 (one cell column
each, built with a helper like `_driver()`); monitoring (2x INA3221); MCU + LDO + diode-OR + buttons; key switch,
fuse, boost, `J_PWR1`; mounting holes.

**Step:** `make BOARD=pack sch`. `gen_sch.py` reports layout clashes with their location; move parts until it
writes `pack.kicad_sch` and `check_netlist.py` prints `netlist matches design.py`. Open `pack.kicad_sch` in
KiCad and eyeball it once. Commit.

### Task P3.2: ERC clean

`make BOARD=pack sch` then
`kicad-cli sch erc --severity-all --exit-code-violations -o build/pack_erc.rpt pack.kicad_sch`.
Fix every violation in `pack.py` (missing no-connects, power-input pins without a driver: add `PWR_FLAG`-style
handling the same way the carrier does for its rails). Expect exit code 0. Commit.

---

## Phase P4: pack PCB

### Task P4.1: Outline and placement

**Files:** `pack.py`: `W`, `H` (from the holder courtyard measured in P0, about 90 x 85 mm), `CORNER`, `PLACE`,
`REF_AT`, `LABELS`, `TEXTS = [("AirsoftCounter v2 pack", ...), ("2026-10", ...)]`, `GND_VIAS = []`,
`HELTEC_PADS = {}`, `NETCLASS_EXPECT`.

Placement rules (design doc, "Mechanical and assembly"):
- Four holders side by side, top side, THT; every SMD part on the top side in the free strip (single-side
  assembly).
- Charger, inductor, boost away from the cells; each NTC directly under its cell's middle.
- Per-cell chain beside its holder's + end, in branch order, so the four branches are copies of each other.
- `J_USB1` and `J_PWR1` and `J_KEY1` on board edges; `SW_BOOT`, `SW_RST` reachable with the pack closed if
  possible.
- Holes at the corners, matching the ZP240.190 plate if P0 found the pattern.

**Step:** `make BOARD=pack pcb`. Expect `wrote pack.kicad_pcb`. Open it and check overlaps. Commit.

### Task P4.2: Route, DRC, fab

**Step 1:** `make BOARD=pack check` (Freerouting, then ERC + DRC with schematic parity). Fix placement until DRC
is clean. Power nets get the 0.8 mm `Power` class through `NETCLASS_POWER`; the shunt Kelvin sense lines
(`CELLi_F`/`CELLi_S` to the INA3221) must leave the shunt pads, not the power track: if Freerouting does not do
this, add the sense nets as separate nets through a 0R or net-tie (decide here, note it in `pack.py`).

**Step 2:** `make BOARD=pack fab`. `check_gerbers.py` must pass with the pack's size and holes; `jlc.py` writes
`fab/pack/jlc_bom.csv` and `fab/pack/jlc_cpl.csv`. Check the CPL rotation of U_CHG, U_MCU, U_INA*, J_USB1 in
JLC's preview later (list them in `ORDERING.md`).

**Step 3:** `make boards` to confirm the carrier still builds. Commit:
`hardware: pack board layout and fab package`.

---

## Phase P5: carrier power moves off

### Task P5.1: Carrier netlist

**Files:** `hardware/design.py`.

- Remove `J_BAT1`, `J_KEY1`, `F1`, `U4`, `R_PROT1`, `C_PROT1`, `U1`, `L1`, `D1`, `R_FB1`, `R_FB2`, `C_IN1`,
  `C_OUT1`, `C_OUT2` from `PARTS`, `NETS`, `LCSC` (only the entries no remaining part uses: `check()` reports
  stale ones), `XH_SPARE`, `NC_PINS` (`U1.6`), `NETCLASS_POWER` (`BAT_N`, `SW`).
- Delete nets `VBAT_RAW`, `BAT_N`, `PROT_VDD`, `VBAT_F`, `SW`, `FB`; remove their pins from `GND`.
- Add `J_PWR1` (`"PWR"`, `Connector_Generic:Conn_01x06`, 6-pin XH footprint) with its LCSC number from P0:
  `J_PWR1.1`, `J_PWR1.2` on `GND`; `J_PWR1.3` on `VBAT_SW`; `J_PWR1.4` on `+5V`; `J_PWR1.5` on `SDA_3V3`;
  `J_PWR1.6` on `SCL_3V3`.
- Keep `J_HBAT1` and `C_BULK1/2` on `VBAT_SW`. Update the U4 comment block (board GND is now the pack ground).

**Step:** `/usr/bin/python3 design.py` -> `design ok`. Commit.

### Task P5.2: Carrier layout

Update `BLOCKS` (the "Battery, key switch, 5 V boost" block becomes "Power in (from pack board)": `J_PWR1`,
`J_HBAT1`, `C_BULK1/2`), `PLACE` (`J_PWR1` on the top edge where `J_BAT1`/`J_KEY1` were: a 6-pin XH courtyard is
about 18.5 mm, the two freed 13.5 mm slots give 29 mm), `REF_AT`, `LABELS` (`"J_PWR1": ("PACK", "GND GND BAT 5V SDA SCL")`).

**Step:** `make all`. Expect ERC/DRC clean and a new `fab/` package. Check the top render (`fab/top.png`).
Commit: `hardware: carrier takes power from the pack board (J_PWR1)`.

---

## Phase P6: power model and docs

### Task P6.1: `power_budget.py`

- `CELLS_MAH = 4 * 3350`.
- Add a pack quiescent line (`PACK_IQ_MA`, EST from P0: LDO + MCU Stop + 2x INA3221 power-down + BQ25601
  battery-only + 4 x 4 uA gate resistors) to the key-off case, and the about 150 mOhm branch drop (negligible at
  these currents: state it in a comment instead of modelling it).
- Run `/usr/bin/python3 power_budget.py` and paste the new runtime figures into the design doc and the status
  memory. Commit.

### Task P6.2: Docs

- `fab/ORDERING.md`: two boards, per-order Extended setup fees for the pack (BQ25601, STM32C071, INA3221,
  XB8089D x1 part type, inductor, USB-C, 6-pin XH, ...), the 6-pin XH on the carrier, parts to check in JLC's
  rotation preview.
- `fab/OFFBOARD_PARTS.md`: 4x INR18650-35E (matched, one batch), 4 holders (hand-soldered), 6-pin XH cable
  (straight 1:1, pin 1 to pin 1), key switch lead now goes to the pack.
- `docs/plans/2026-09-28-esp32-lora-carrier-design.md`: one line under the power section pointing to the pack
  board doc (power section superseded).
- Update `docs/plans/2026-10-01-pack-board-design.md` status line: hardware done, firmware deferred.

Commit: `docs: pack board ordering and off-board parts`.

---

## Done when

- `make boards` is green (ERC, DRC with parity, Gerber check, JLC files) for both boards.
- `/usr/bin/python3 pack.py` and `/usr/bin/python3 board.py` pass.
- Design doc "Unverified" holds only what needs real hardware.
