kkrzysztofik/ASG_AirsoftCounter/hardware/fab/offboard/tme_offboard.csv

V19-11R-06R-S | 1
V19-11R-06B-S | 1
BZ-38 | 1
VS-K50-8 | 1
82-6121.2000 | 1
GSM-IPX/SMA-150 | 1
ANT-868-CW-RCS-SMA | 1
ZP240.190.105SJP TM ABSPC | 1
ZP240.190-PCB | 1
RFID-GW-NTAG213 | 10
