kkrzysztofik/ASG_AirsoftCounter/hardware/fab/offboard/tme_offboard_crimp.csv

XHP-6 | 3
XHP-4 | 5
XHP-2 | 5
SXH-001T-P0.6 | 30
MX-51021-0200 | 1
MX-50079-8000 | 4
