kkrzysztofik/ASG_AirsoftCounter/hardware/fab/bottom.png

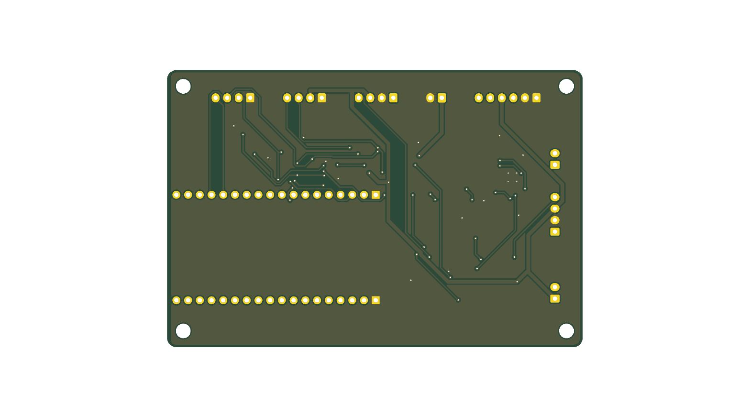
hardware/fab/bottom.png
