kkrzysztofik/ASG_AirsoftCounter/hardware/fab/carrier_tme/top.png

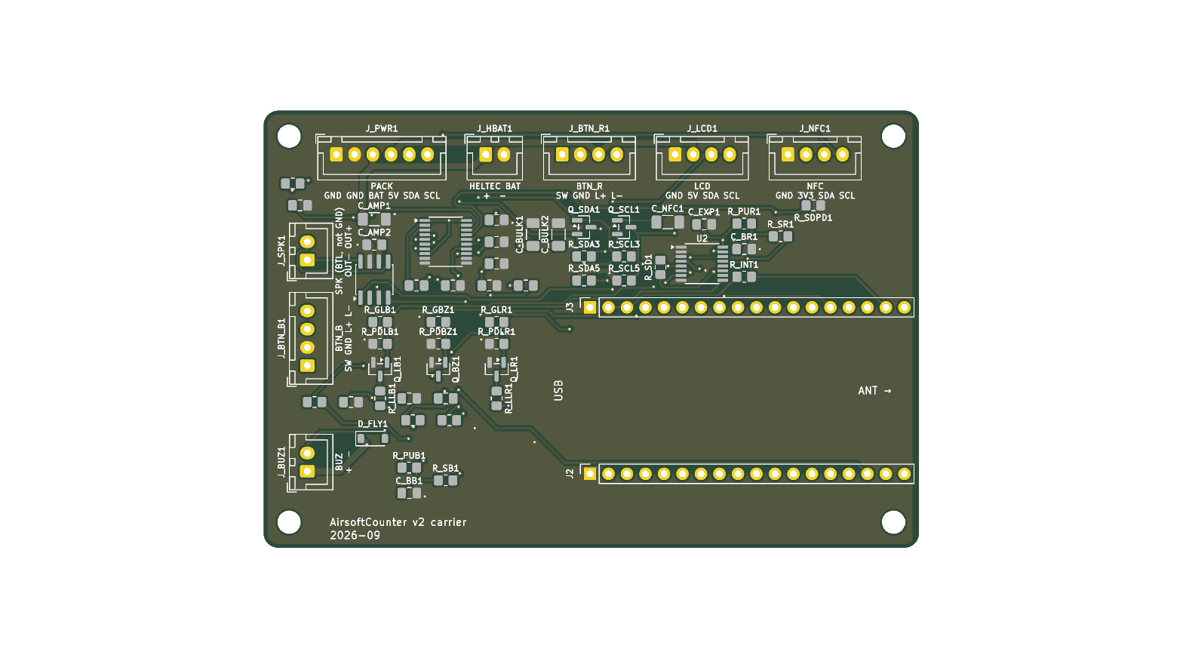
hardware/fab/carrier_tme/top.png
