kkrzysztofik/ASG_AirsoftCounter/hardware/fab/lipo/top.png

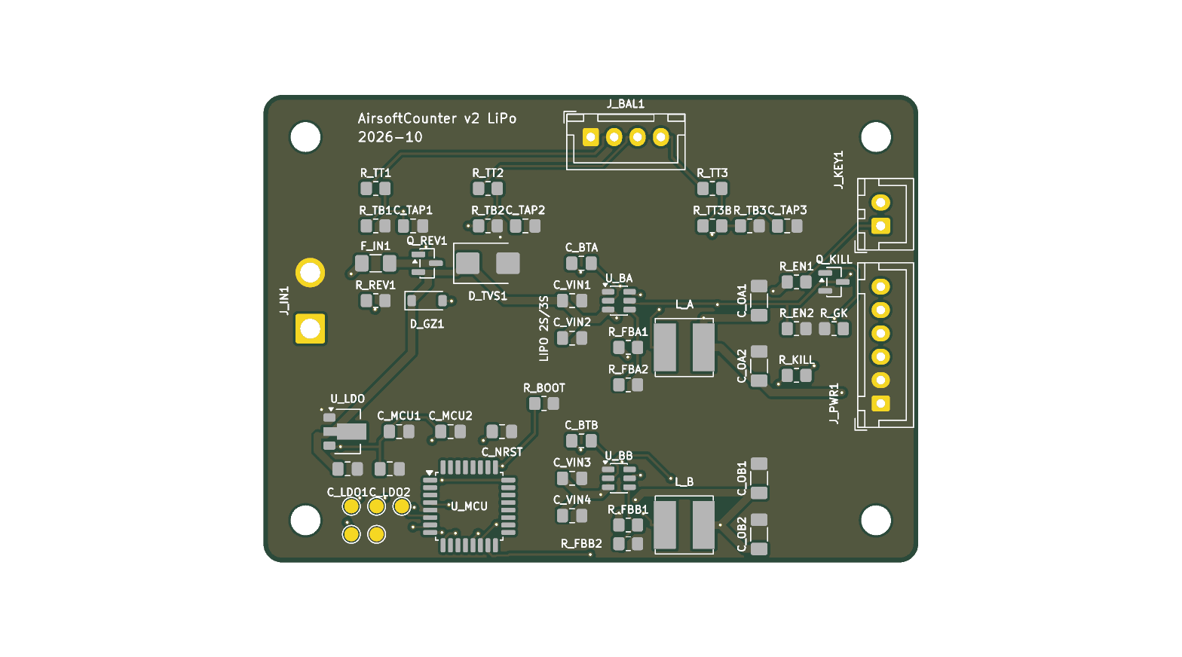
hardware/fab/lipo/top.png
