kkrzysztofik/ASG_AirsoftCounter/hardware/fab/pack/bottom.png

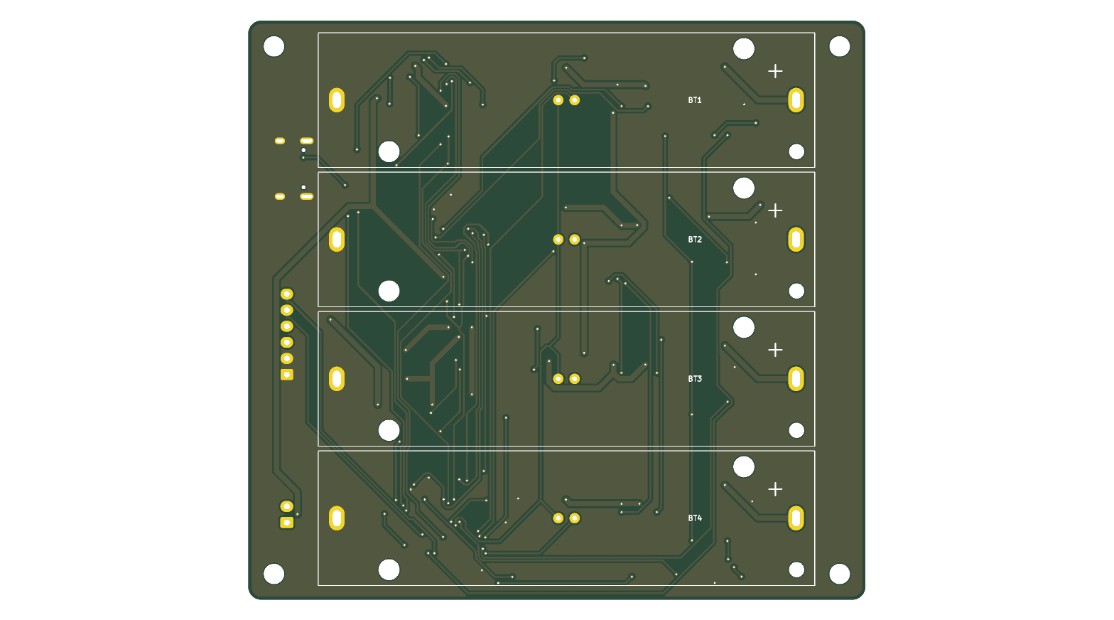
hardware/fab/pack/bottom.png
