kkrzysztofik/ASG_AirsoftCounter/hardware/fab/pack/top.png

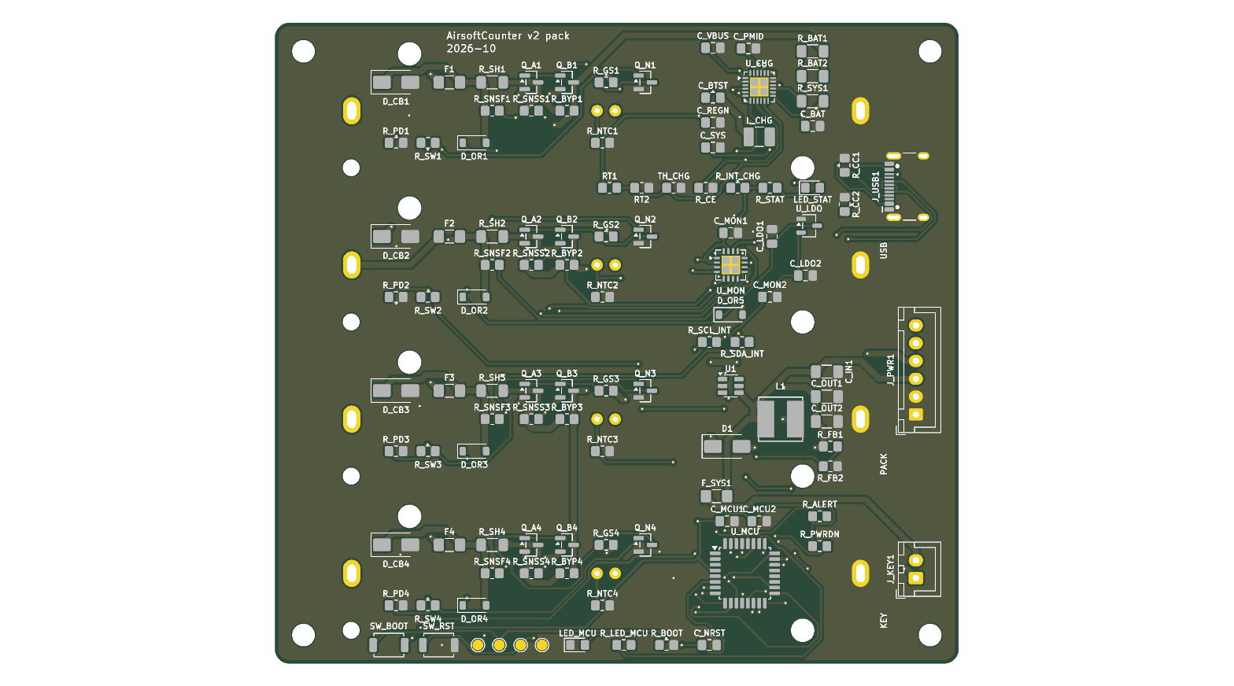
hardware/fab/pack/top.png
