kkrzysztofik/ASG_AirsoftCounter/hardware/fab/pack_b/bottom.png

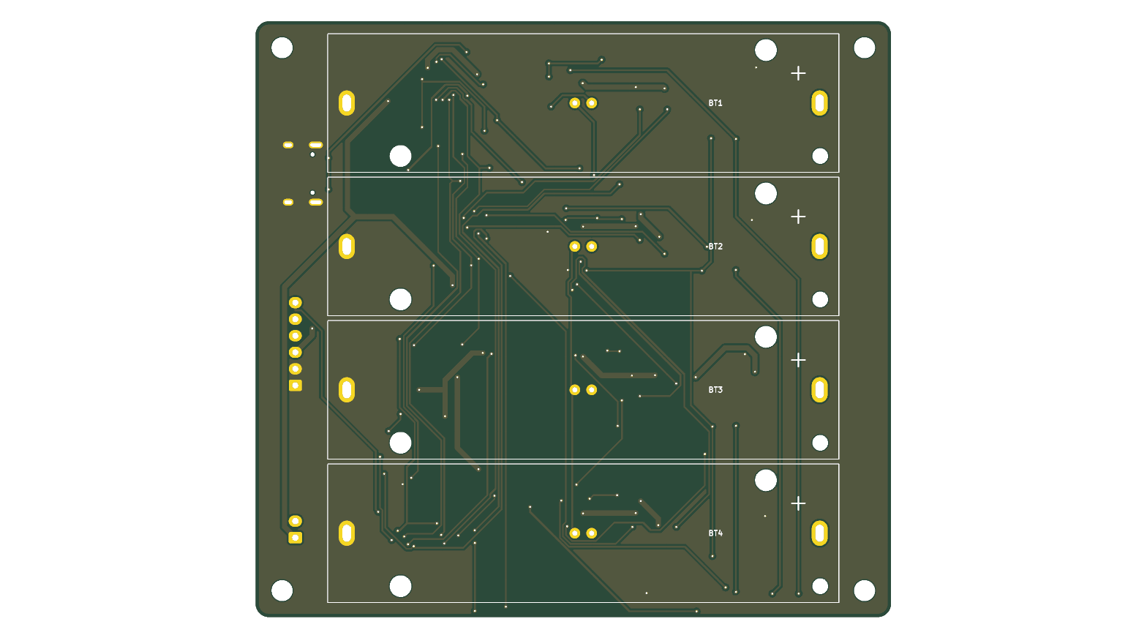
hardware/fab/pack_b/bottom.png
