kkrzysztofik/ASG_AirsoftCounter/hardware/fab/pack_b/top.png

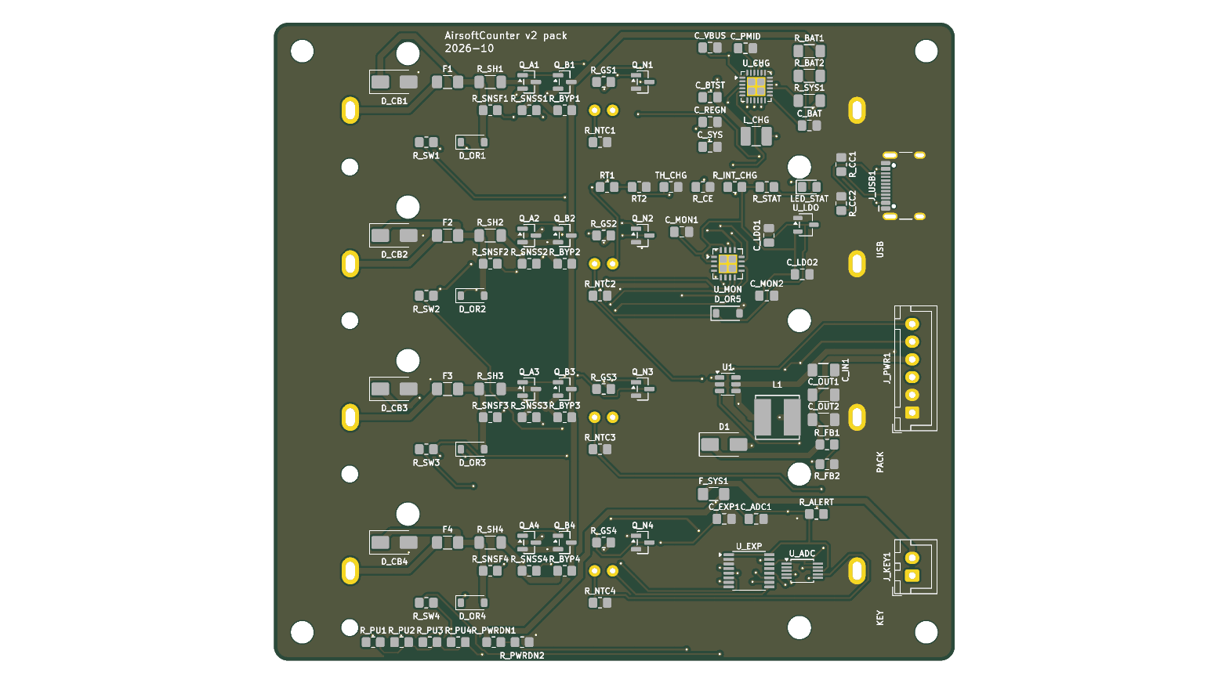
hardware/fab/pack_b/top.png
