kkrzysztofik/ASG_AirsoftCounter/hardware/fab/pack_tme/bottom.png

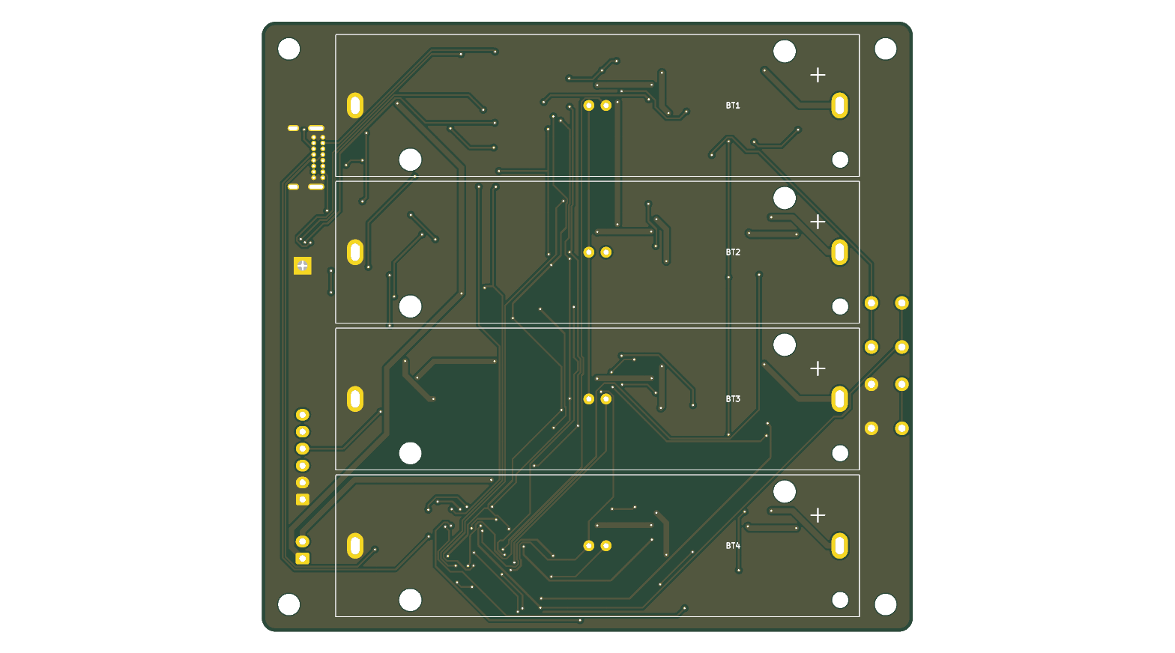
hardware/fab/pack_tme/bottom.png
