kkrzysztofik/ASG_AirsoftCounter/hardware/fab/placed_top.png

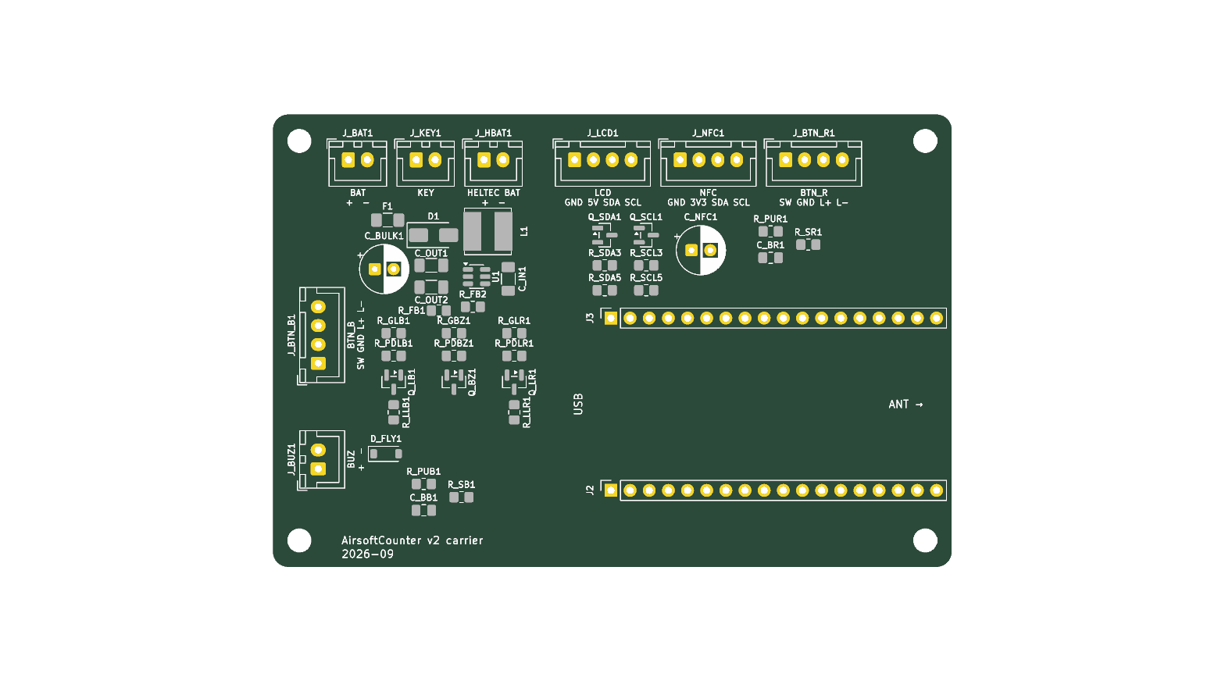
hardware/fab/placed_top.png
