kkrzysztofik/ASG_AirsoftCounter/hardware/fab/bom.csv

Refs | Value | Footprint | Qty
C_AMP1,C_NFC1 | 100uF 6.3V | Capacitor_SMD:C_1206_3216Metric_Pad1.33x1.80mm_HandSolder | 2
C_AMP2,C_BB1,C_BR1,C_EXP1 | 100nF | Capacitor_SMD:C_0805_2012Metric_Pad1.18x1.45mm_HandSolder | 4
C_BULK1,C_BULK2 | 47uF 10V | Capacitor_SMD:C_1206_3216Metric_Pad1.33x1.80mm_HandSolder | 2
D_FLY1 | 1N4148W | Diode_SMD:D_SOD-123 | 1
J2 | Heltec_J2 | Connector_PinSocket_2.54mm:PinSocket_1x18_P2.54mm_Vertical | 1
J3 | Heltec_J3 | Connector_PinSocket_2.54mm:PinSocket_1x18_P2.54mm_Vertical | 1
J_BTN_B1 | BTN_B | Connector_JST:JST_XH_B4B-XH-A_1x04_P2.50mm_Vertical | 1
J_BTN_R1 | BTN_R | Connector_JST:JST_XH_B4B-XH-A_1x04_P2.50mm_Vertical | 1
J_BUZ1 | BUZ | Connector_JST:JST_XH_B2B-XH-A_1x02_P2.50mm_Vertical | 1
J_HBAT1 | HELTEC_BAT | Connector_JST:JST_XH_B2B-XH-A_1x02_P2.50mm_Vertical | 1
J_LCD1 | LCD | Connector_JST:JST_XH_B4B-XH-A_1x04_P2.50mm_Vertical | 1
J_NFC1 | NFC | Connector_JST:JST_XH_B4B-XH-A_1x04_P2.50mm_Vertical | 1
J_PWR1 | PWR | Connector_JST:JST_XH_B6B-XH-A_1x06_P2.50mm_Vertical | 1
J_SPK1 | SPK | Connector_JST:JST_XH_B2B-XH-A_1x02_P2.50mm_Vertical | 1
Q_BZ1,Q_LB1,Q_LR1,Q_SCL1,Q_SDA1 | BSS138 | Package_TO_SOT_SMD:SOT-23 | 5
R_GBZ1,R_GLB1,R_GLR1,R_SB1,R_SD1,R_SR1 | 1k | Resistor_SMD:R_0805_2012Metric_Pad1.20x1.40mm_HandSolder | 6
R_INT1,R_PDBZ1,R_PDLB1,R_PDLR1,R_PUB1,R_PUR1,R_SDPD1 | 10k | Resistor_SMD:R_0805_2012Metric_Pad1.20x1.40mm_HandSolder | 7
R_LLB1,R_LLR1 | 0R | Resistor_SMD:R_0805_2012Metric_Pad1.20x1.40mm_HandSolder | 2
R_SCL3,R_SDA3 | 4k7 | Resistor_SMD:R_0805_2012Metric_Pad1.20x1.40mm_HandSolder | 2
U2 | TCA9534PWR | Package_SO:TSSOP-16_4.4x5mm_P0.65mm | 1
U3 | NS4168 | Package_SO:HSOP-8-1EP_3.9x4.9mm_P1.27mm_EP2.3x2.3mm_ThermalVias | 1
