kkrzysztofik/ASG_AirsoftCounter/hardware/fab/pack_tme/bom.csv

Refs | Value | Footprint | Qty
C_BAT?,C_PMID?,C_SYS?,C_VBUS? | 10uF | Capacitor_SMD:C_0805_2012Metric_Pad1.18x1.45mm_HandSolder | 4
C_BTST? | 47nF | Capacitor_SMD:C_0805_2012Metric_Pad1.18x1.45mm_HandSolder | 1
C_IN1,C_OUT1,C_OUT2 | 22uF 25V | Capacitor_SMD:C_1206_3216Metric_Pad1.33x1.80mm_HandSolder | 3
C_LDO1,C_LDO2,C_VDDA? | 1uF | Capacitor_SMD:C_0805_2012Metric_Pad1.18x1.45mm_HandSolder | 3
C_MCU1,C_MCU3,C_MON1-C_MON4,C_NRST? | 100nF | Capacitor_SMD:C_0805_2012Metric_Pad1.18x1.45mm_HandSolder | 7
C_MCU2,C_REGN? | 4u7 | Capacitor_SMD:C_0805_2012Metric_Pad1.18x1.45mm_HandSolder | 2
D_CB1-D_CB4 | SS34 | Diode_SMD:D_SMA | 4
D_OR1-D_OR5 | B5819W | Diode_SMD:D_SOD-123 | 5
F1-F4 | 5A fuse | Fuse:Fuse_1206_3216Metric_Pad1.42x1.75mm_HandSolder | 4
F_SYS1 | 2A PTC | Fuse:Fuse_1206_3216Metric_Pad1.42x1.75mm_HandSolder | 1
J_KEY1 | KEY | Connector_JST:JST_XH_B2B-XH-A_1x02_P2.50mm_Vertical | 1
J_PWR1 | PWR | Connector_JST:JST_XH_B6B-XH-A_1x06_P2.50mm_Vertical | 1
J_USB1 | USB4085-GF-A | Connector_USB:USB_C_Receptacle_GCT_USB4085 | 1
L1 | 3u3 | Inductor_SMD:L_Bourns_SRN6045TA | 1
LED_MCU? | green | LED_SMD:LED_0805_2012Metric_Pad1.15x1.40mm_HandSolder | 1
LED_STAT? | red | LED_SMD:LED_0805_2012Metric_Pad1.15x1.40mm_HandSolder | 1
L_CHG? | 1u5 | Inductor_SMD:L_1210_3225Metric_Pad1.42x2.65mm_HandSolder | 1
Q_A1-Q_A4,Q_B1-Q_B4 | AO3401A | Package_TO_SOT_SMD:SOT-23 | 8
Q_N1-Q_N4 | BSS138 | Package_TO_SOT_SMD:SOT-23 | 4
RT1,R_CC1,R_CC2 | 5k1 | Resistor_SMD:R_0805_2012Metric_Pad1.20x1.40mm_HandSolder | 3
RT2 | 30k | Resistor_SMD:R_0805_2012Metric_Pad1.20x1.40mm_HandSolder | 1
R_ALERT?,R_BOOT?,R_CE?,R_INT_CHG?,R_NTC1-R_NTC4 | 10k | Resistor_SMD:R_0805_2012Metric_Pad1.20x1.40mm_HandSolder | 8
R_BAT1,R_BAT2,R_SYS1 | 0R | Resistor_SMD:R_1206_3216Metric_Pad1.30x1.75mm_HandSolder | 3
R_FB1 | 75k | Resistor_SMD:R_0805_2012Metric_Pad1.20x1.40mm_HandSolder | 1
R_FB2 | 24k | Resistor_SMD:R_0805_2012Metric_Pad1.20x1.40mm_HandSolder | 1
R_GS1-R_GS4 | 1M | Resistor_SMD:R_0805_2012Metric_Pad1.20x1.40mm_HandSolder | 4
R_LED_MCU?,R_STAT?,R_SW1-R_SW4 | 1k | Resistor_SMD:R_0805_2012Metric_Pad1.20x1.40mm_HandSolder | 6
R_PD1-R_PD4 | 100k | Resistor_SMD:R_0805_2012Metric_Pad1.20x1.40mm_HandSolder | 4
R_SCL_INT?,R_SDA_INT? | 4k7 | Resistor_SMD:R_0805_2012Metric_Pad1.20x1.40mm_HandSolder | 2
R_SH1-R_SH4 | 10mOhm | Resistor_SMD:R_1206_3216Metric_Pad1.30x1.75mm_HandSolder | 4
R_SNSF1-R_SNSF4,R_SNSS1-R_SNSS4 | 10R | Resistor_SMD:R_0805_2012Metric_Pad1.20x1.40mm_HandSolder | 8
SW_BOOT?,SW_RST? | TACT 6x6 | Button_Switch_THT:SW_PUSH_6mm | 2
TH_CHG? | 10k NTC 0603 | Resistor_SMD:R_0805_2012Metric_Pad1.20x1.40mm_HandSolder | 1
U1 | MCP1640T-I/CHY | Package_TO_SOT_SMD:SOT-23-6 | 1
U_CHG? | BQ25601RTWT | local:QFN-24-1EP_4x4mm_P0.5mm_EP2.6x2.6mm_HandSolder | 1
U_LDO? | XC6206P332MR | Package_TO_SOT_SMD:SOT-23-3 | 1
U_MCU? | STM32L072KZT6 | Package_QFP:LQFP-32_7x7mm_P0.8mm | 1
U_MON1-U_MON4 | INA226AIDGSR | Package_SO:VSSOP-10_3x3mm_P0.5mm | 4
