kkrzysztofik/ASG_AirsoftCounter/hardware/fab/lipo/schematic.pdf

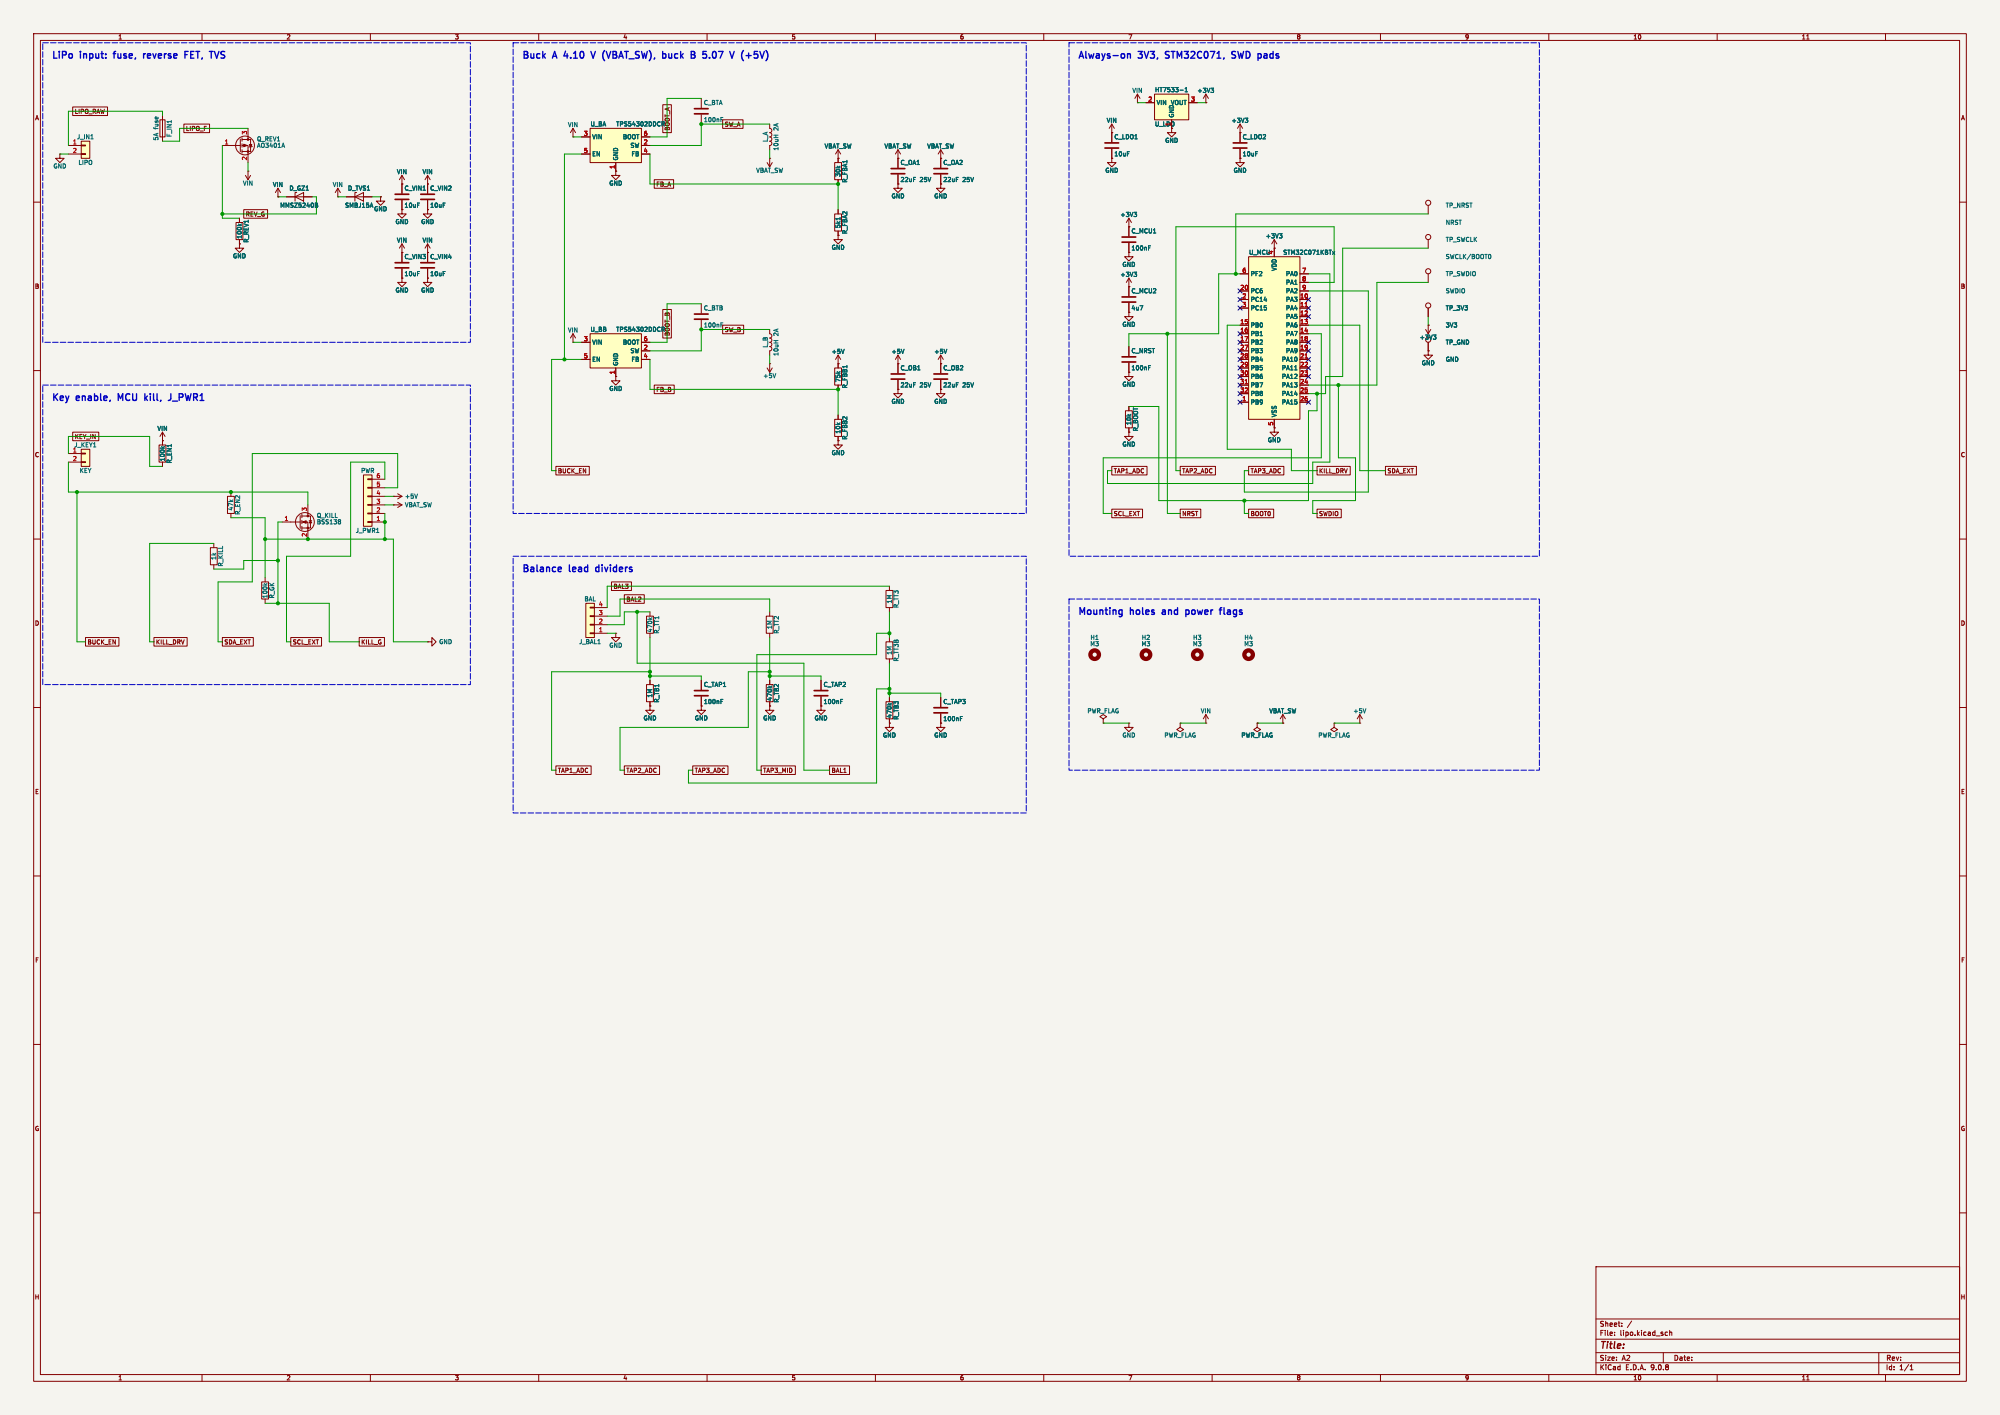
[picture p20: page 1]

1 BOOT 6 SW 2 FB 4 VIN U_BB TPS54302DDCR GND F_IN1 5A fuse C_VIN2

GND GND

1 BOOT 6 SW 2 FB 4 GND

Key enable, MCU kill, J_PWR1
