kkrzysztofik/ASG_AirsoftCounter/hardware/fab/lipo/print_1to1.pdf

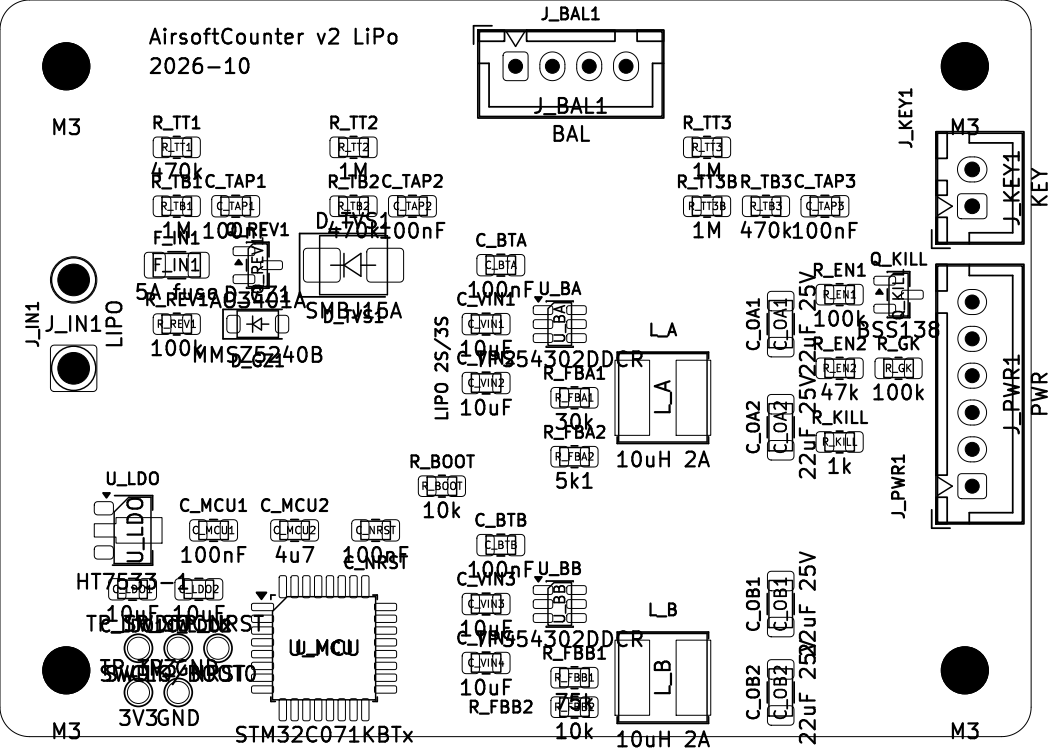
[picture p27: page 1]
