kkrzysztofik/ASG_AirsoftCounter/firmware/device/src/bin/main.rs

#![no_std]
#![no_main]
#![deny(
    clippy::mem_forget,
    reason = "mem::forget is generally not safe to do with esp_hal types, especially those \
    holding buffers for the duration of a data transfer."
)]
#![deny(clippy::large_stack_frames)]

use asg_device::board::{self, Board};
use embassy_executor::Spawner;
use embassy_time::{Duration, Timer};
use esp_backtrace as _;
use esp_hal::clock::CpuClock;
use esp_hal::gpio::{Level, Output, OutputConfig};
use esp_hal::timer::timg::TimerGroup;
use log::info;

// This creates a default app-descriptor required by the esp-idf bootloader.
// For more information see: <https://docs.espressif.com/projects/esp-idf/en/stable/esp32/api-reference/system/app_image_format.html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>
esp_bootloader_esp_idf::esp_app_desc!();

#[allow(clippy::large_stack_frames, reason = "it's not unusual to allocate larger buffers etc. in main")]
#[esp_rtos::main]
async fn main(_spawner: Spawner) -> ! {
    // generator version: 1.4.0
    // generator parameters: -o esp32s3 -o unstable-hal -o embassy -o log -o esp-backtrace

    esp_println::logger::init_logger_from_env();

    let config = esp_hal::Config::default().with_cpu_clock(CpuClock::max());
    let board = Board::new(esp_hal::init(config));

    let timg0 = TimerGroup::new(board.timg0);
    esp_rtos::start(timg0.timer0, board.sw_int0);

    let game = asg_core::game::Config::default();
    info!("asg-core linked, default block size {}", game.block_size);

    let mut led = Output::new(board.onboard_led, Level::Low, OutputConfig::default());
    info!("blinking onboard LED on GPIO{}", board::ONBOARD_LED);
    loop {
        info!("alive");
        led.set_high();
        Timer::after(Duration::from_millis(500)).await;
        led.set_low();
        Timer::after(Duration::from_millis(500)).await;
    }
}
